Shreyankkkkk/foundations/projects/sumo-robot/notes/chat-summaries/INDEX.md

# Sumo chat summaries: index

Raw summaries (as generated by the summary prompt, one file per account): `account-1-context.txt` (18 chats), `account-2-context.txt` (15 chats). Both files are in this folder, unchanged except for any personal lines removed by hand.
`Order` is inferred from cross-references, not dates. Fill `Date` from the chat sidebar, then move the matching LOG.md lines into the dated section.
ID = account + position in that account's file.

| Order | ID | Chat title | Phase | Date |
|---|---|---|---|---|
| 1 | A1-10 | SumoX-26 Robot Planning | 1 planning | |
| 2 | A1-09 | SumoX-26 robot coding intro | 1 planning | |
| 3 | A1-01 | SumoX-26 Parts List & Sourcing | 1 planning | |
| 4 | A2-01 | Sumo Robot Strategy Selection | 1 planning | |
| 5 | A2-02 | Sumo robot GitHub research kickoff | 1 planning | |
| 6 | A1-02 | Sumo robot prep review | 1 planning | |
| 7 | A1-08 | SumoX-26 UNO Q wiring map | 2 wiring | |
| 8 | A1-03 | SumoX-26 constants and file architecture | 2 wiring | |
| 9 | A1-07 | SumoX-26 UNO Q firmware | 2 wiring | |
| 10 | A2-03 | SumoX-26 code audit & fixes | 3 Hybrid | |
| 11 | A2-04 | SumoX-26 firmware audit & merge | 3 Hybrid | |
| 12 | A1-04 | SumoX-26 code review and rewrite | 3 Hybrid | |
| 13 | A1-05 | SumoX-26 firmware review | 3 Hybrid | |
| 14 | A2-05 | SumoX-26 Code Audit | 3 Hybrid | |
| 15 | A1-06 | SumoX-26 firmware simulator | 3 Hybrid | |
| 16 | A1-11 | Sumo chassis STL audit and redesign | 3 Hybrid | |
| 17 | A2-06 | SumoX-26 firmware review and overhaul | 4 sensors | |
| 18 | A1-12 | Sumo robot sensor audit | 4 sensors | |
| 19 | A1-13 | SumoX-26 code audit and sensor calibration | 4 sensors | |
| 20 | A2-07 | Sumo IR sensor calibration | 4 sensors | |
| 21 | A2-08 | GP2Y0A21 calibration and filtering | 4 sensors | |
| 22 | A1-14 | TCRT5000 edge sensor bring-up | 4 sensors | |
| 23 | A2-09 | SumoX-26 v4 code overhaul | 5 v4 Ram | |
| 24 | A1-15 | SumoX-26 ram code review | 5 v4 Ram | |
| 25 | A2-10 | Sumo robot code audit + sensor bring-up | 5 v4 Ram | |
| 26 | A2-11 | Multi-file Arduino sketch deploy | 5 v4 Ram | |
| 27 | A2-12 | Sumo robot code Q&A prep | 5 v4 Ram | |
| 28 | A2-13 | Sumo robot code review | 5 v4 Ram | |
| 29 | A1-16 | SumoX-26 sumo robot, v4 fixes to v5 build | 6 v5 / v2.x | |
| 30 | A2-14 | Sumo robot code and strategy | 6 v5 / v2.x | |
| 31 | A2-15 | Sumo robot code audit and deploy | 6 v5 / v2.x | |
| 32 | A1-17 | SumoX-26 software finalization | 6 v5 / v2.x | |
| 33 | A1-18 | BlindSumo v2.4 to blind strategy | 6 v5 / v2.x | |

Archive rule: keep the old chats until this folder, LOG.md, STATE.md and Retrospective.md are committed and pushed.
