Shreyankkkkk/foundations/certificates/robotics/besomi-sumo-robot-workshop.pdf

# CERTIFICATE

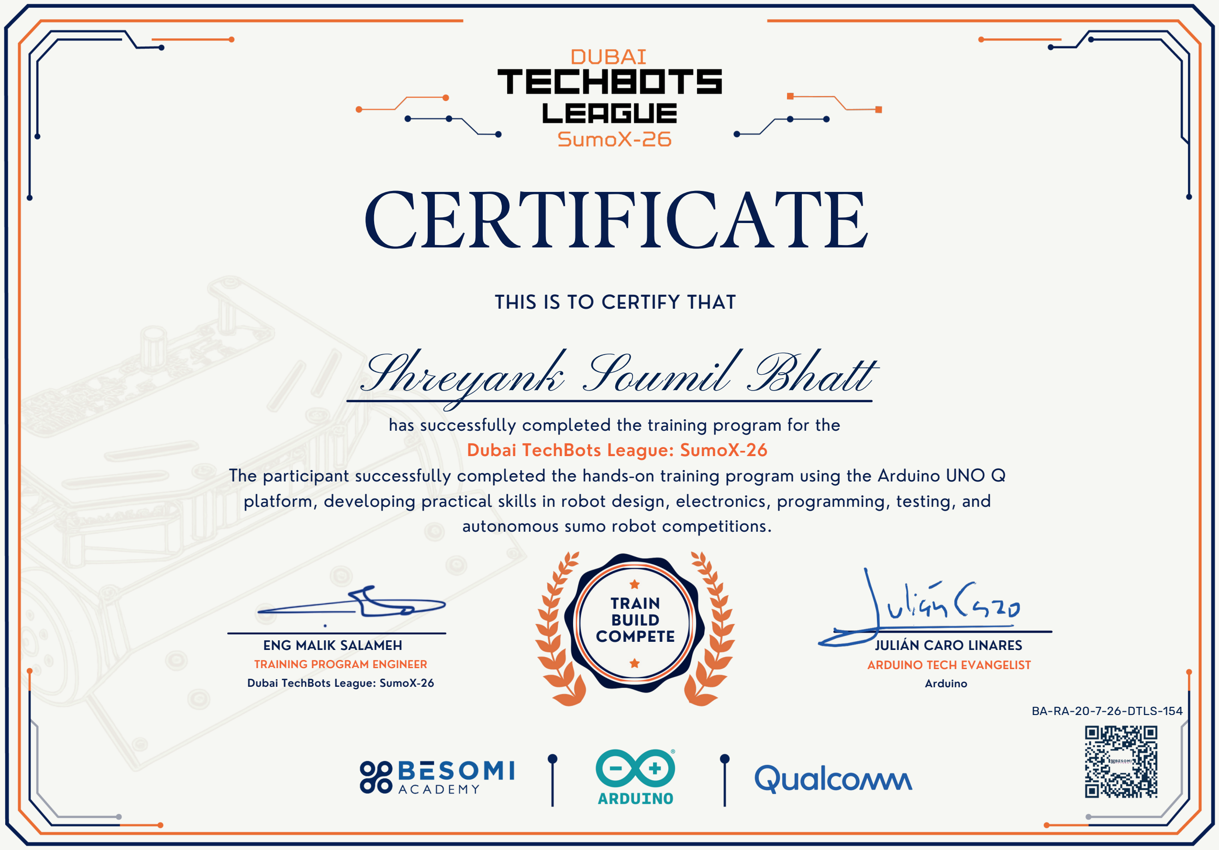
[picture p3: page 1]

TRAIN
BUILD
COMPETE

TRAINING PROGRAM ENGINEER
Dubai TechBots League: SumoX-26 | Arduino
ENG MALIK SALAMEH | JULIÁN CARO LINARES
| ARDUINO TECH EVANGELIST

THIS IS TO CERTIFY THAT

has successfully completed the training program for the Dubai TechBots League: SumoX-26 The participant successfully completed the hands-on training program using the Arduino UNO Q platform, developing practical skills in robot design, electronics, programming, testing, and autonomous sumo robot competitions.

BA-RA-20-7-26-DTLS-154

# Shreyank Soumil Bhatt
