Shreyankkkkk/foundations/projects/sumo-robot/docs/rulebook/Slides Sumo Robot - Dubai Techbots League SumoX-26.pdf

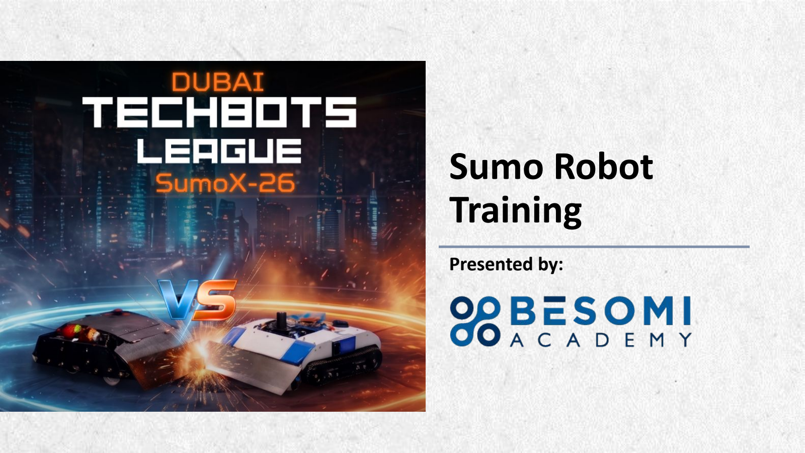
[picture p4: page 1]

# Sumo Robot Training

Presented by:

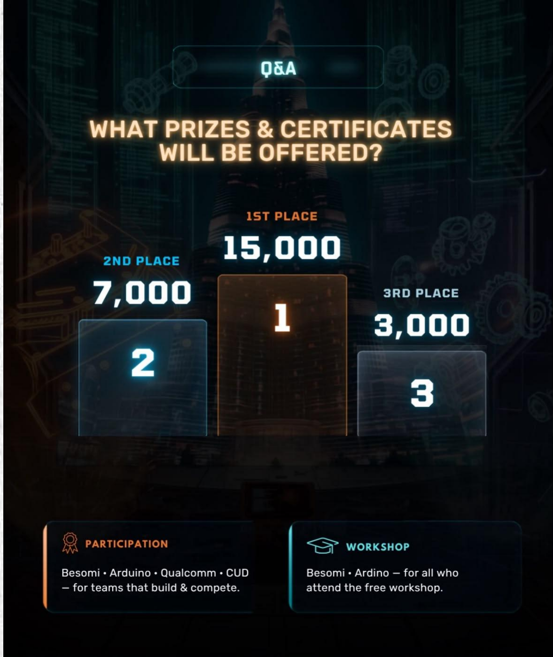
[picture p5: figure]

# Pool Prizes

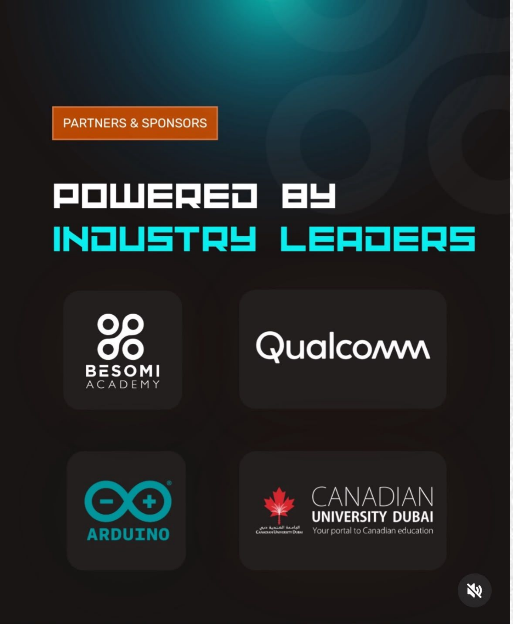
[picture p6: figure]

# POWERED BY

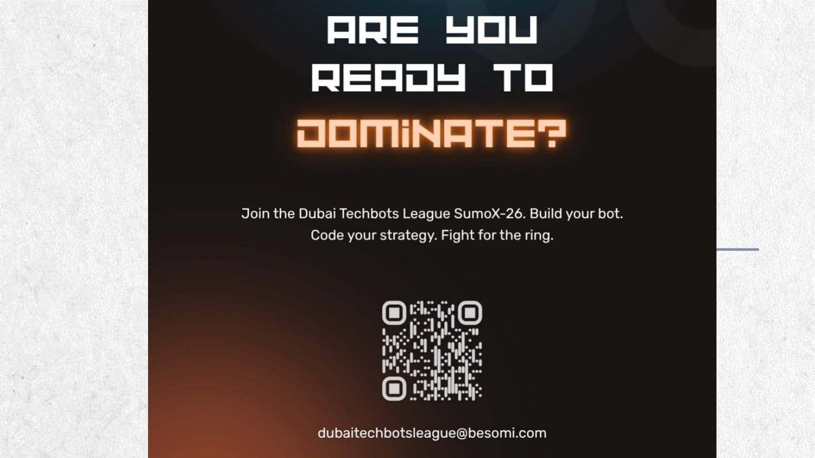
[picture p7: page 4]

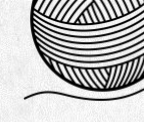
[picture p8: figure]

# LET’S PLAY THE WOOL BALL GAME AND THEN TEAM UP!

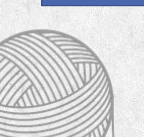
[picture p9: figure]

## WHAT IS SUMO ROBOTS?

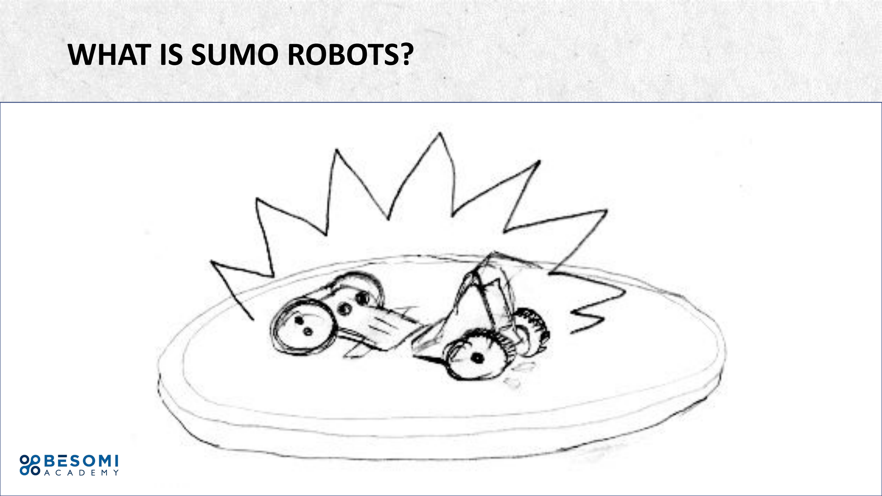
[picture p10: page 6]

## WHAT IS SUMO ROBOTS?

Robot Control: Autonomous and Remote-control

Engineering Principles: Torque, mechanical engineering, electrical engineering, computer science (for autonomous classes.)

Event Summary:
Two robots compete in a head-to-head match following the basic system of traditional human sumo matches. Robots are allowed no weapons, and are not allowed to flip each other. The sole purpose is a pushing match between the two robots to force the other from the arena. Multiple weight classes and control systems are allowed (autonomous compete against autonomous and R/C against R/C -they are separate classes and do not compete against each other.)

## WHAT IS SUMO ROBOTS?

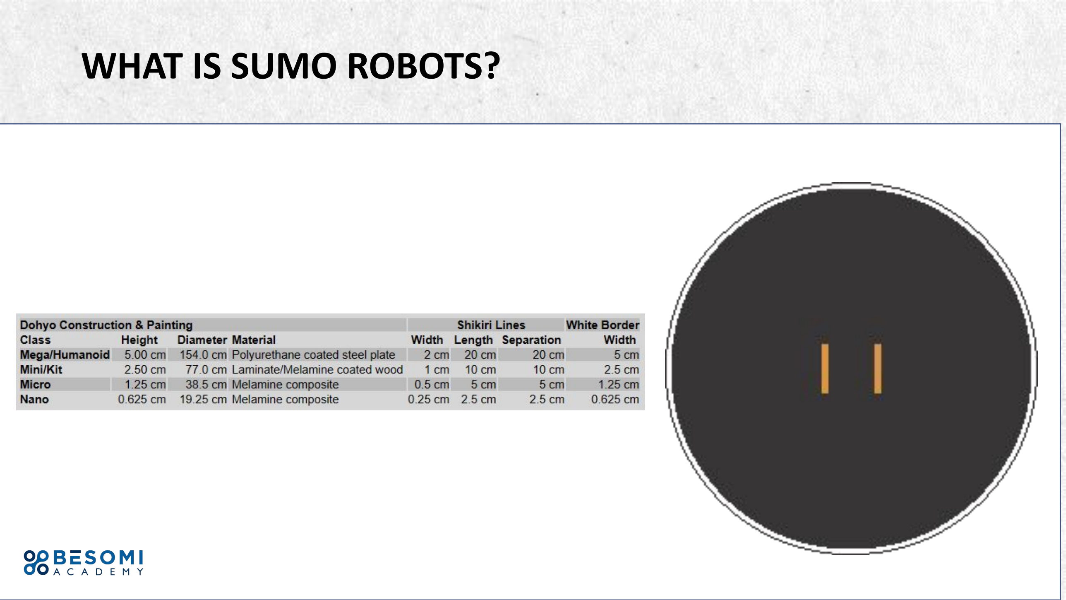
[picture p11: page 8]

## WHAT IS SUMO ROBOTS?

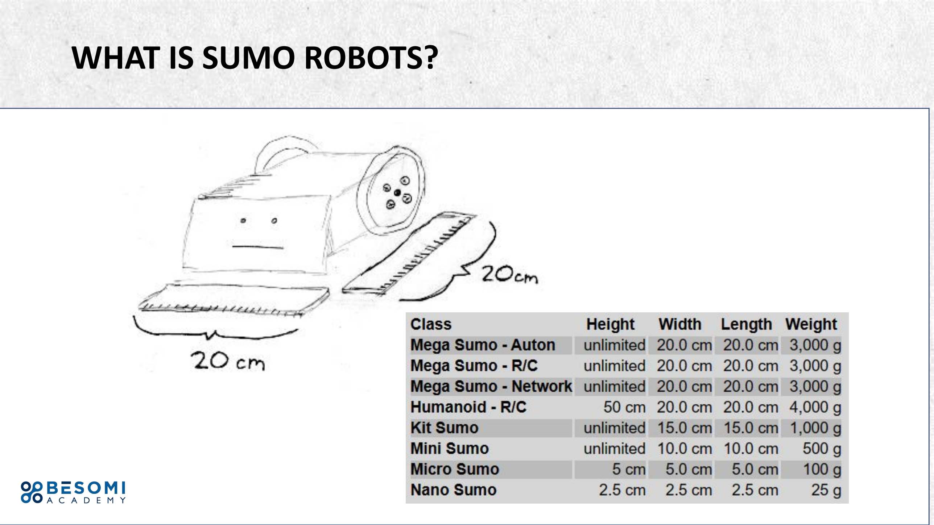
[picture p12: page 9]

## WHAT IS OUR GOAL?

To build an | | trying to fight
autonomous robot | that finds opponents
and push them | out of the ring, and | keep your robot inside the ring.

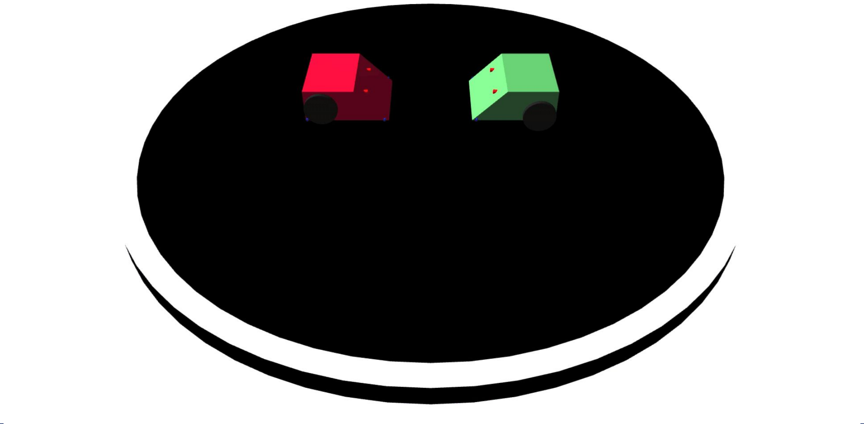
[picture p13: figure]

# What a Sumo Robot Needs?

## What a Sumo Robot Needs?

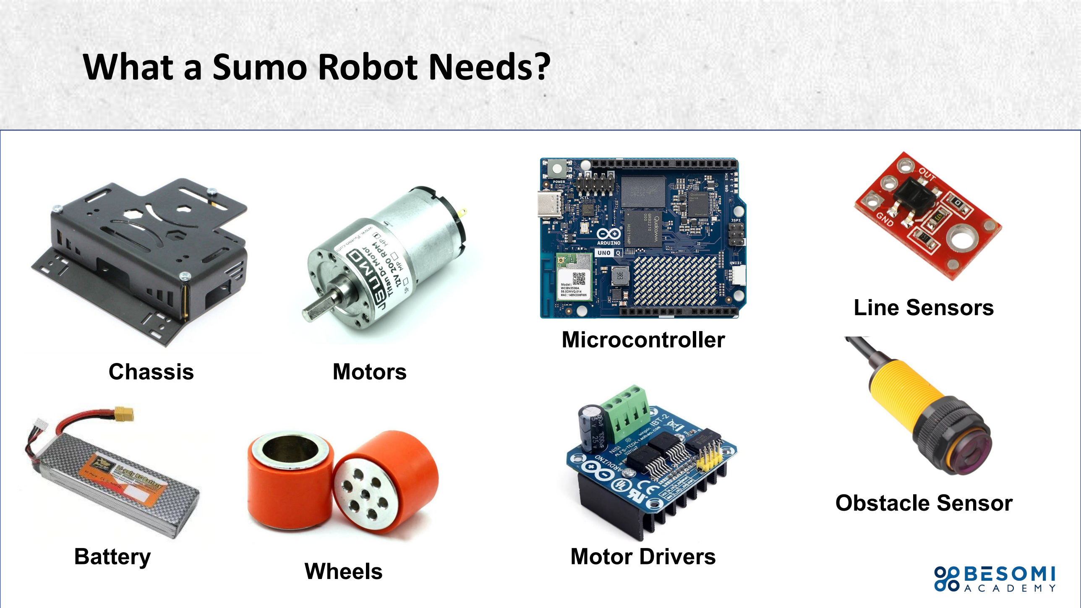
[picture p14: page 12]

Microcontroller

Obstacle Sensor

Line Sensors

Motor Drivers

Chassis

Wheels

Motors

Battery

## WHAT BRAIN TO CHOOSE?

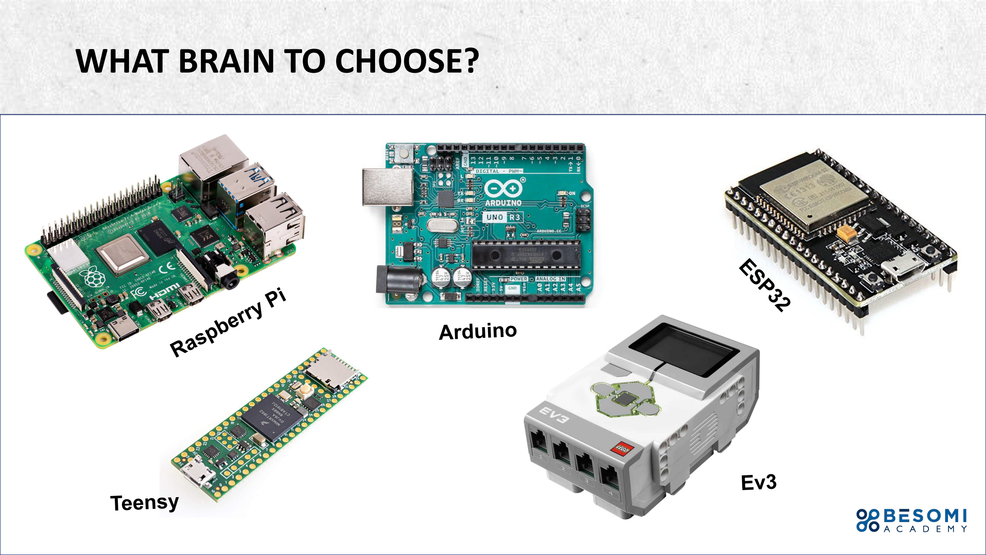
[picture p15: page 13]

Raspberry Pi

Teensy

Arduino

Ev3

ESP32

## TYPES OF ARDUINO BOARDS

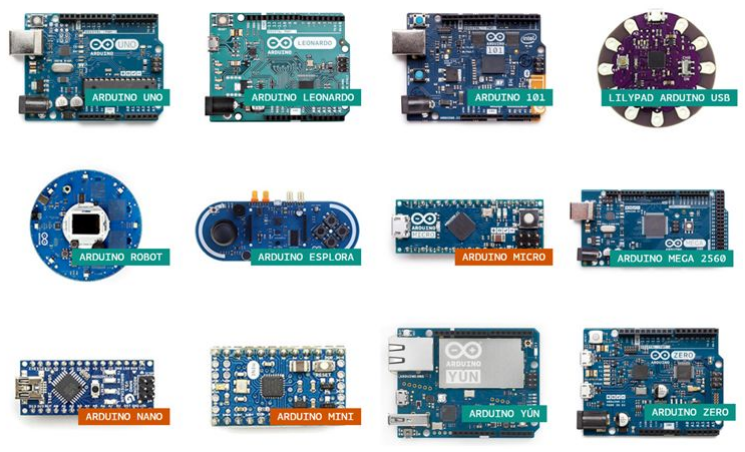
[picture p16: figure]

## OUR CHOICE

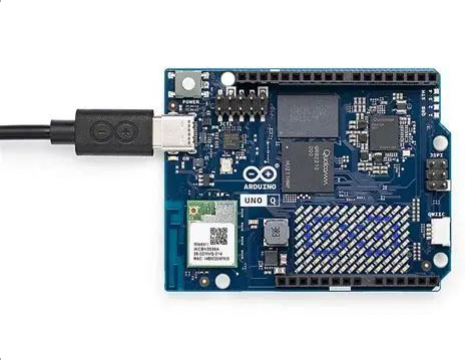
[picture p17: figure]

## Arduino UNO Q

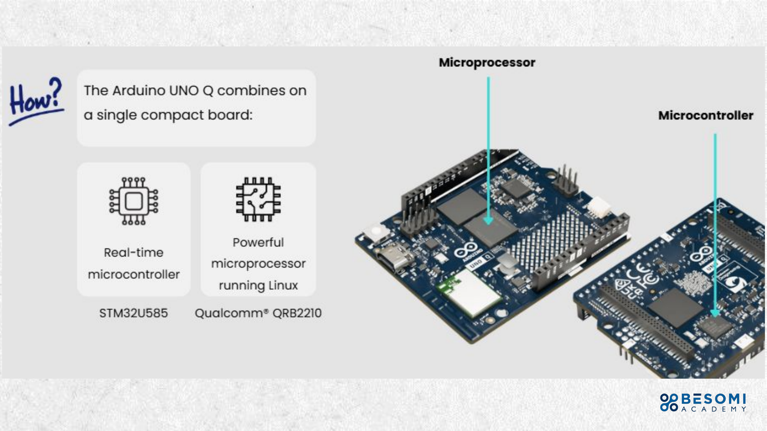
[picture p18: page 16]

## OUR CHOICE

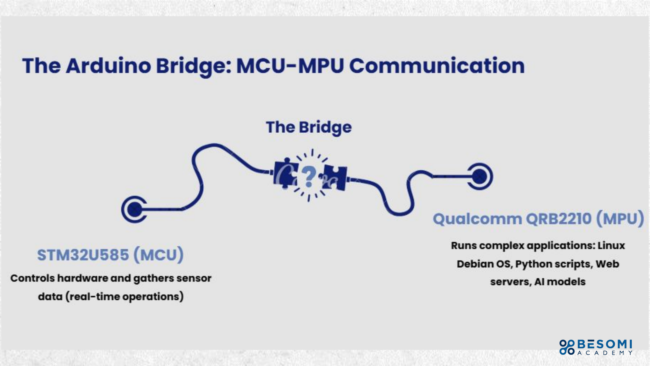
[picture p19: page 17]
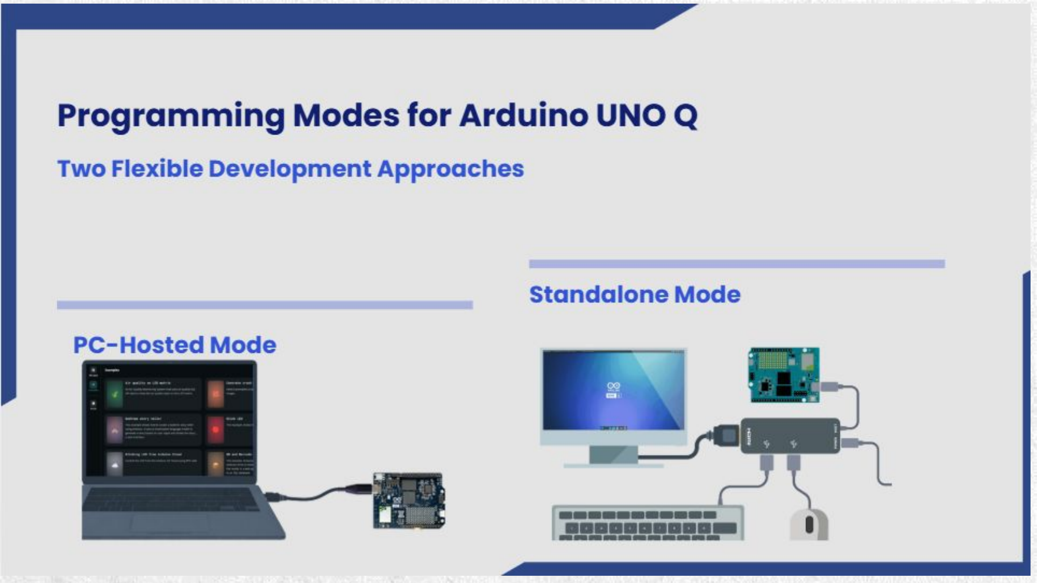
[picture p20: page 18]

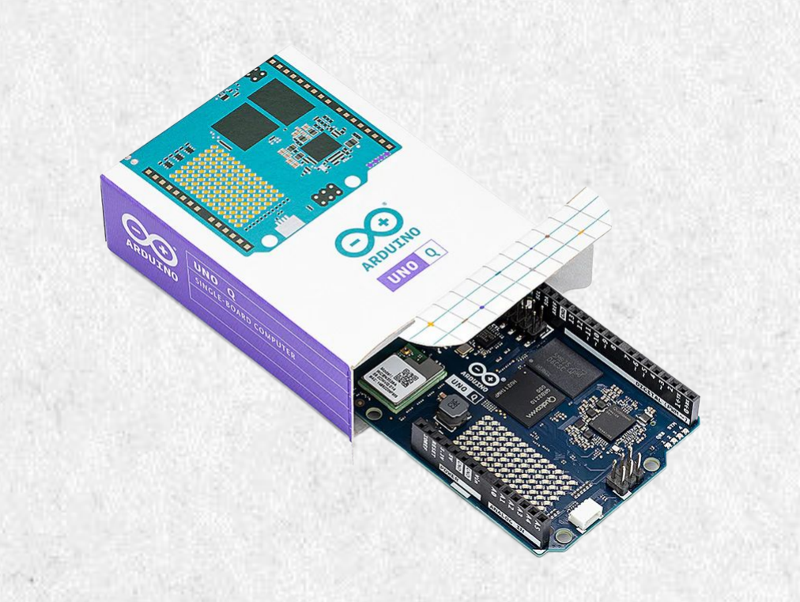
[picture p21: figure]

# WHAT IS ARDUINO?

Arduino is an open-source
electronics platform based on easy-to-use hardware
and software.

## APPLICATIONS OF ARDUINO

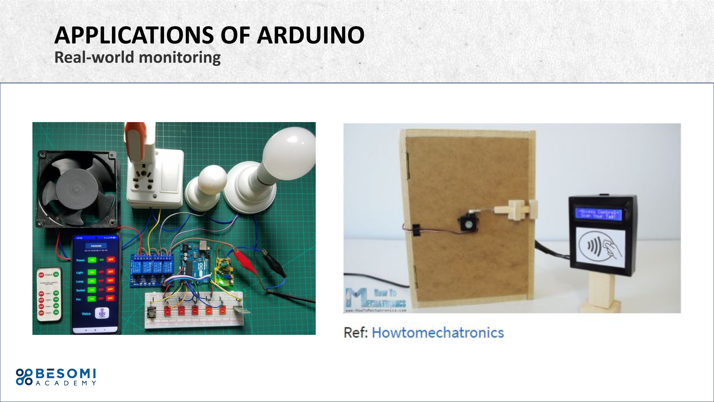
[picture p22: page 20]

Real-world monitoring

## APPLICATIONS OF ARDUINO

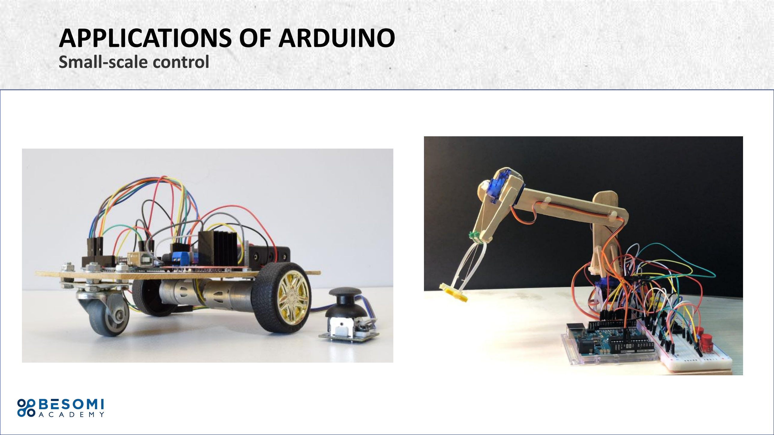
[picture p23: page 21]

Small-scale control

## APPLICATIONS OF ARDUINO

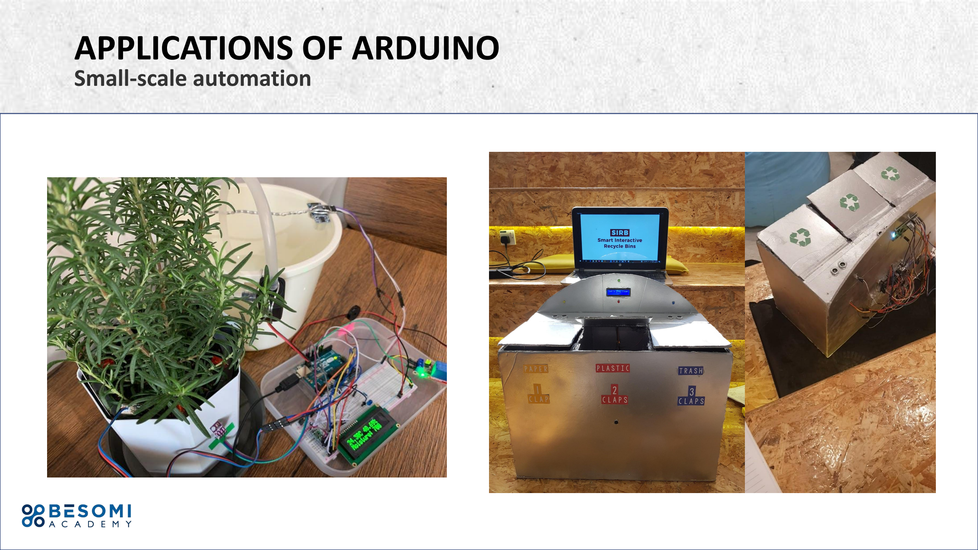
[picture p24: page 22]

Small-scale automation

## APPLICATIONS OF ARDUINO

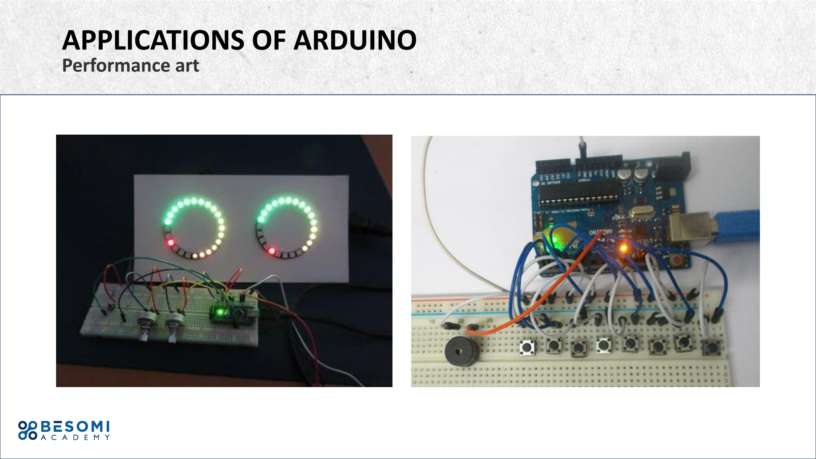
[picture p25: page 23]

Performance art

## TWO WAYS TO PRACTICE WITH US

1

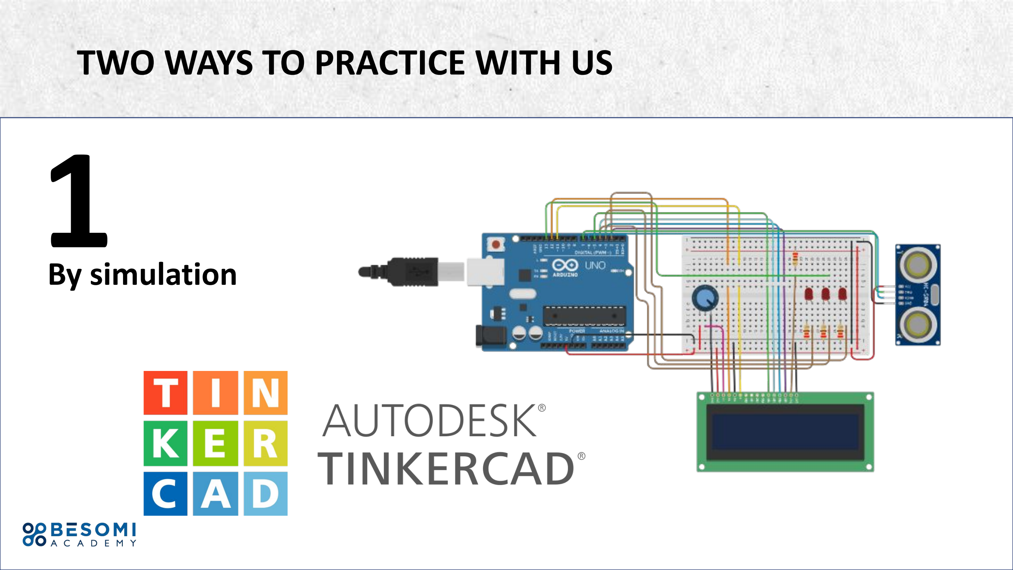
[picture p26: page 24]

## By simulation

## TWO WAYS TO PRACTICE WITH US

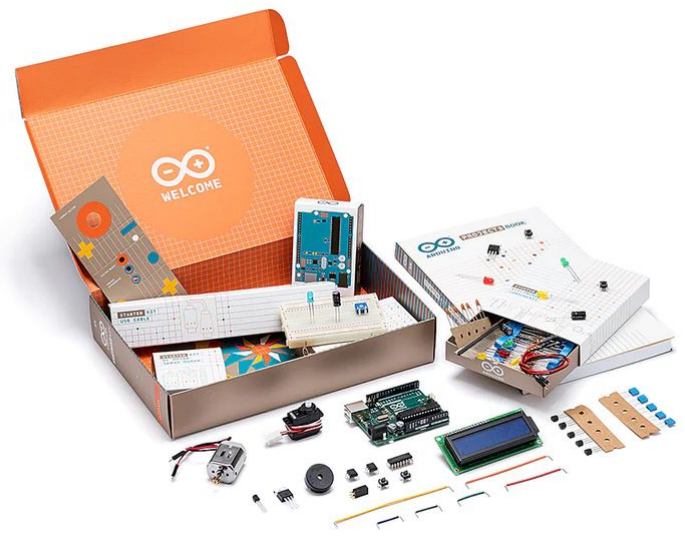
[picture p27: figure]

2

## Physically by hands

## CODING USING ARDUINO IDE

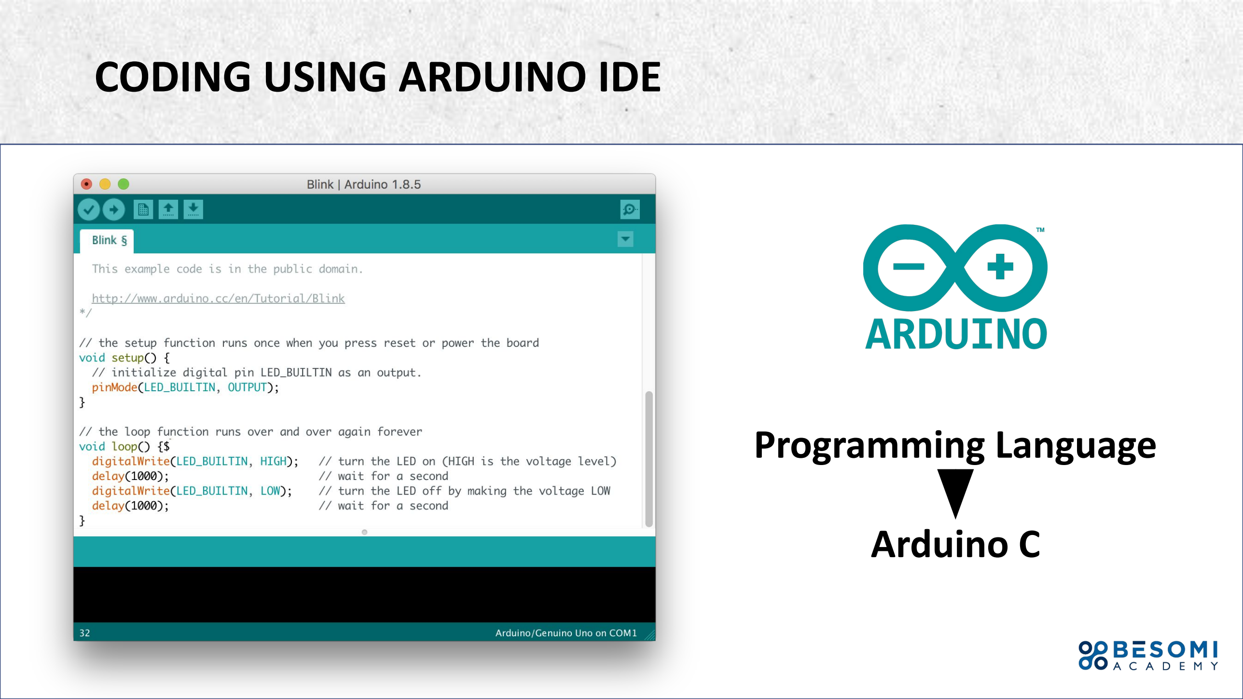
[picture p28: page 26]

## Programming Language

## Arduino C

## Arduino App Lab

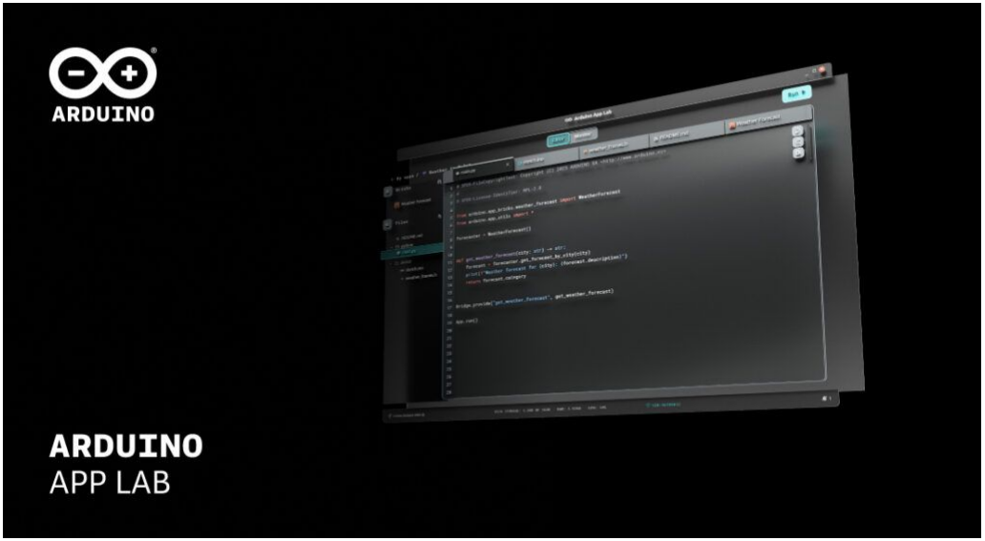
[picture p29: figure]
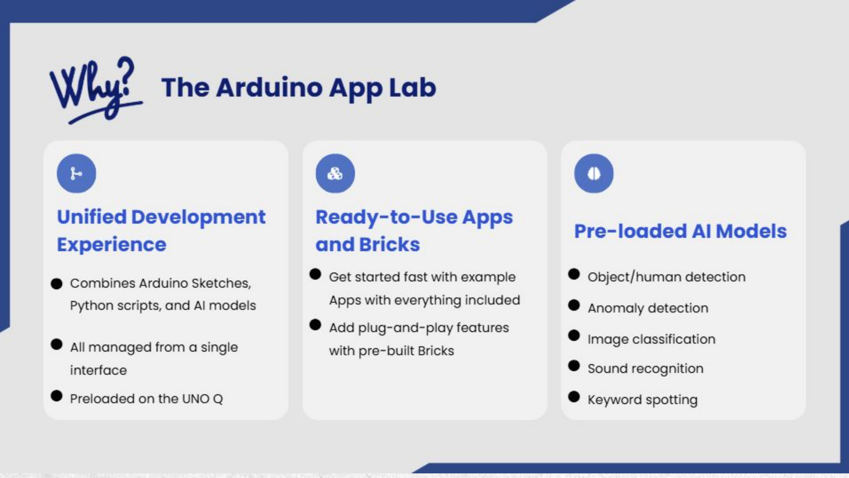
[picture p30: page 28]

# Inputs vs Outputs

## INPUT

VS

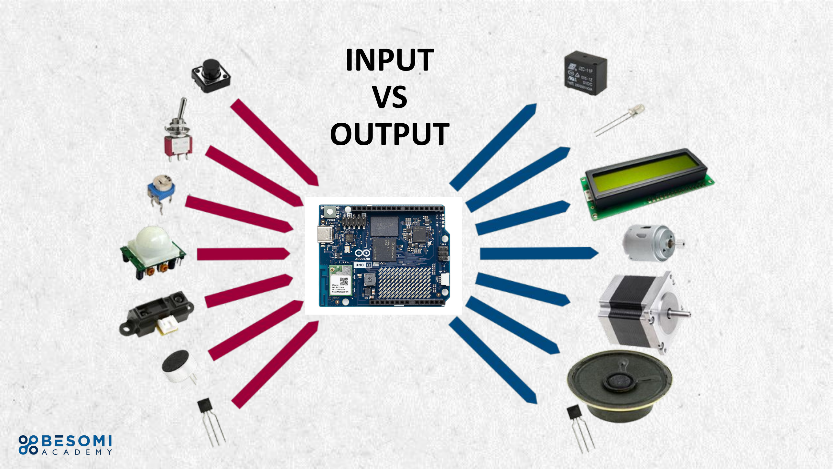
[picture p31: page 30]

## OUTPUT

## INPUT OR OUTPUT?

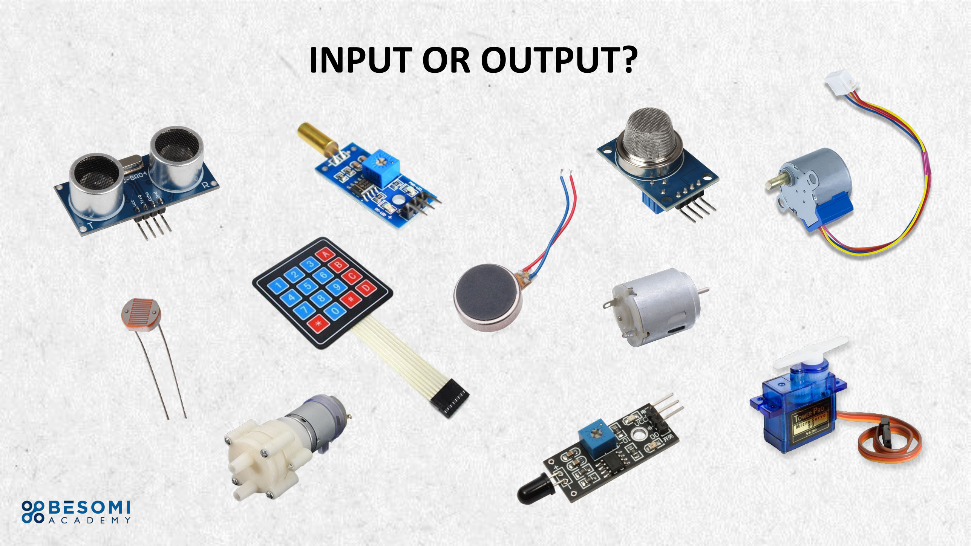
[picture p32: page 31]

# LET’S GET DEEPER

# 3 WAYS TO POWER THE ARDUINO BOARD

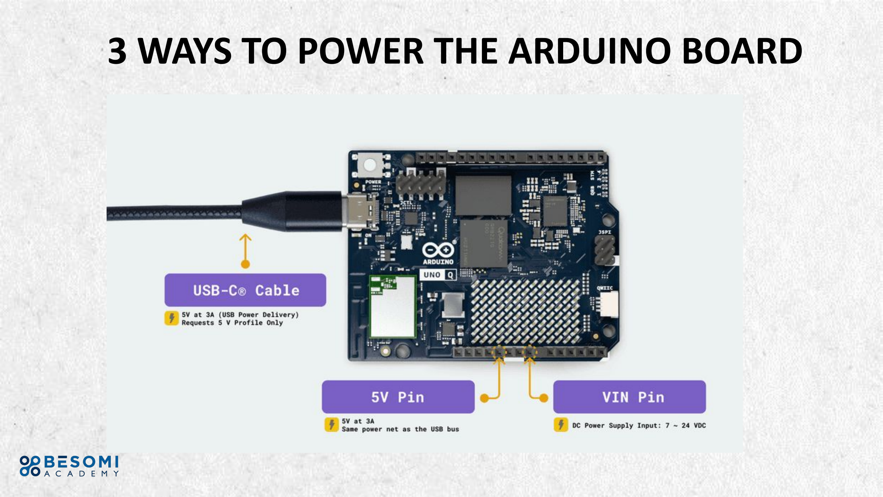
[picture p33: page 33]

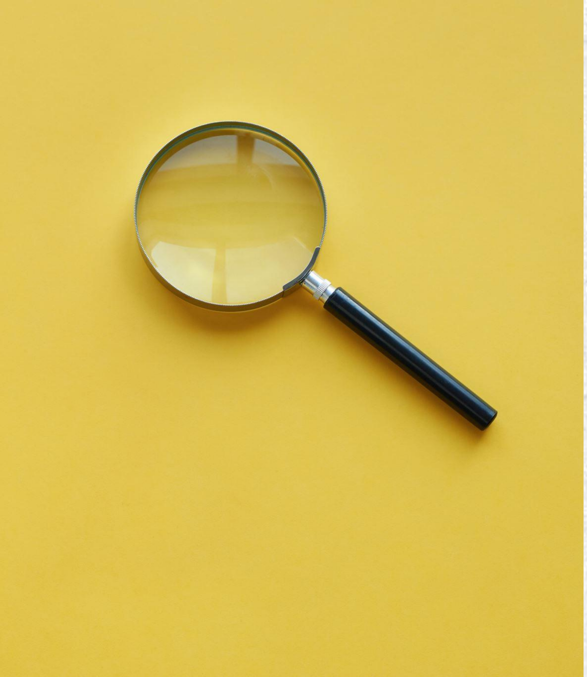
[picture p34: figure]

# FEW THINGS WE SHOULD KNOW ABOUT

## THE BREADBOARD

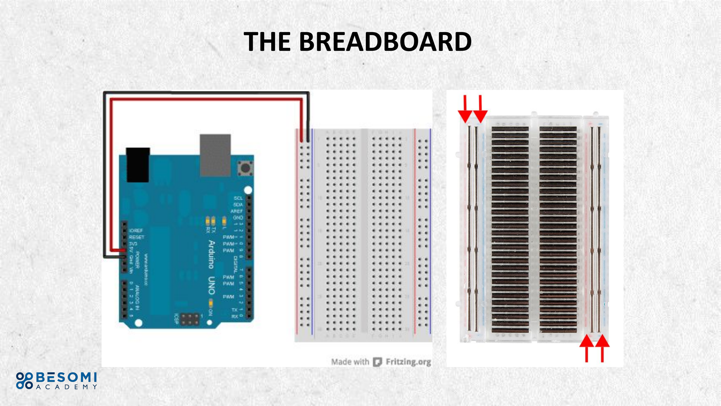
[picture p35: page 35]

# JUMPER WIRES

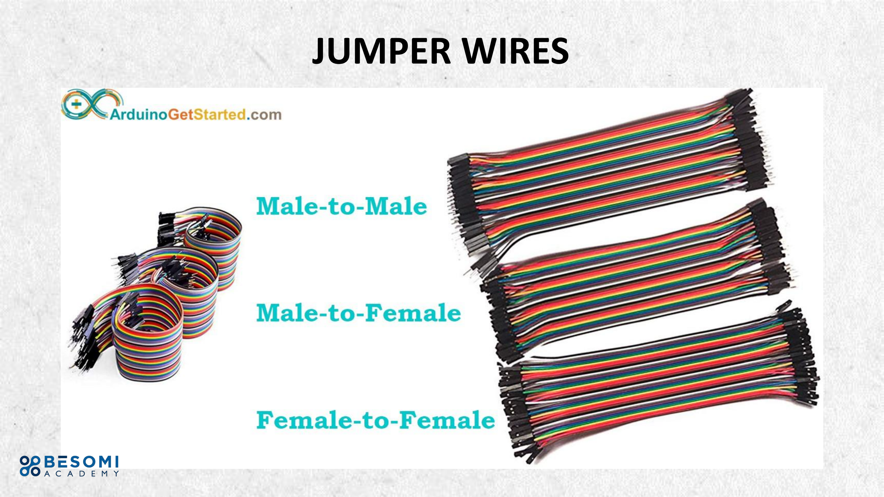
[picture p36: page 36]

## ANODE & CATHODE

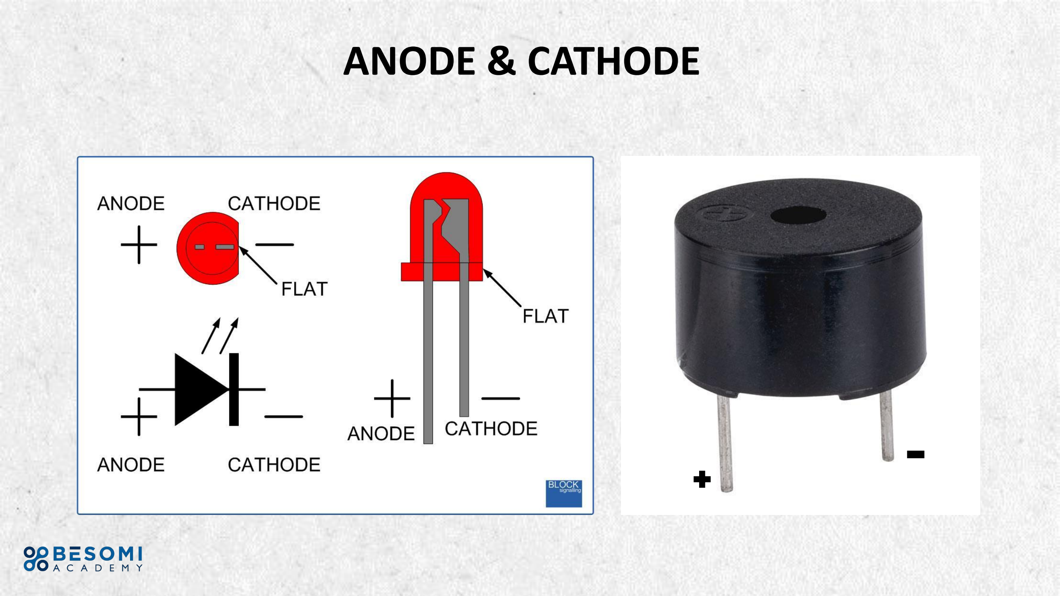
[picture p37: page 37]

## RESISTORS

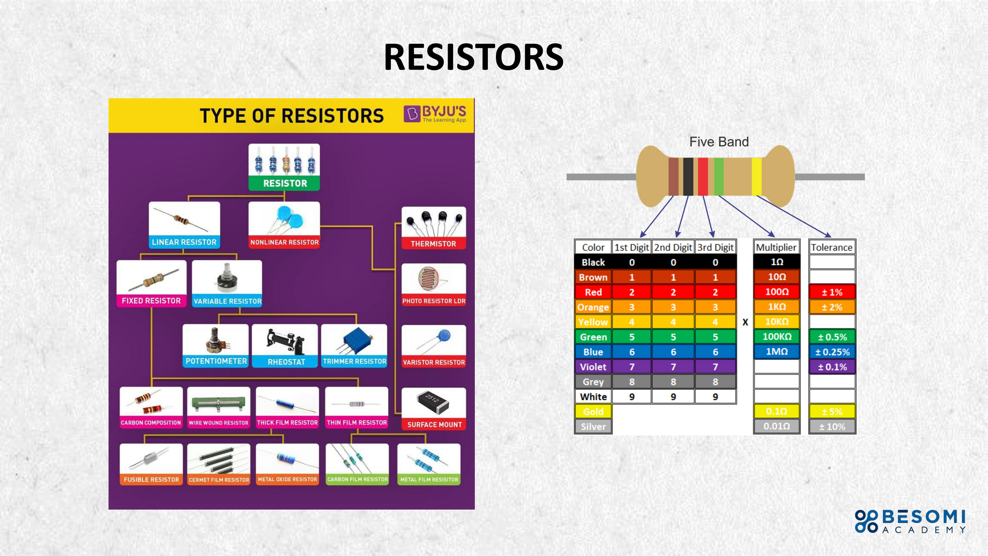
[picture p38: page 38]

# DIGITAL PINS

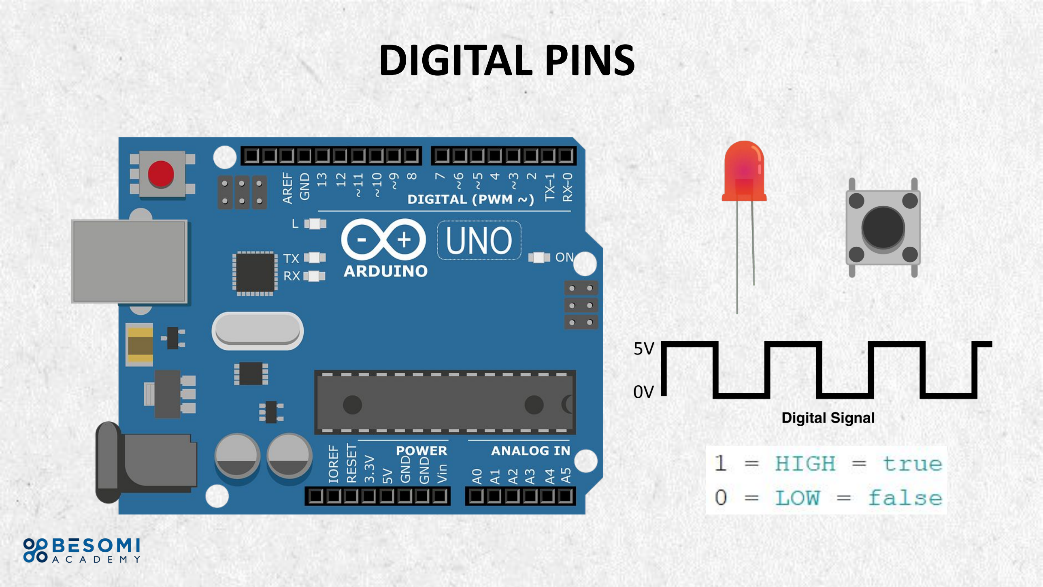
[picture p39: page 39]

5V

0V

# DIGITAL PINS

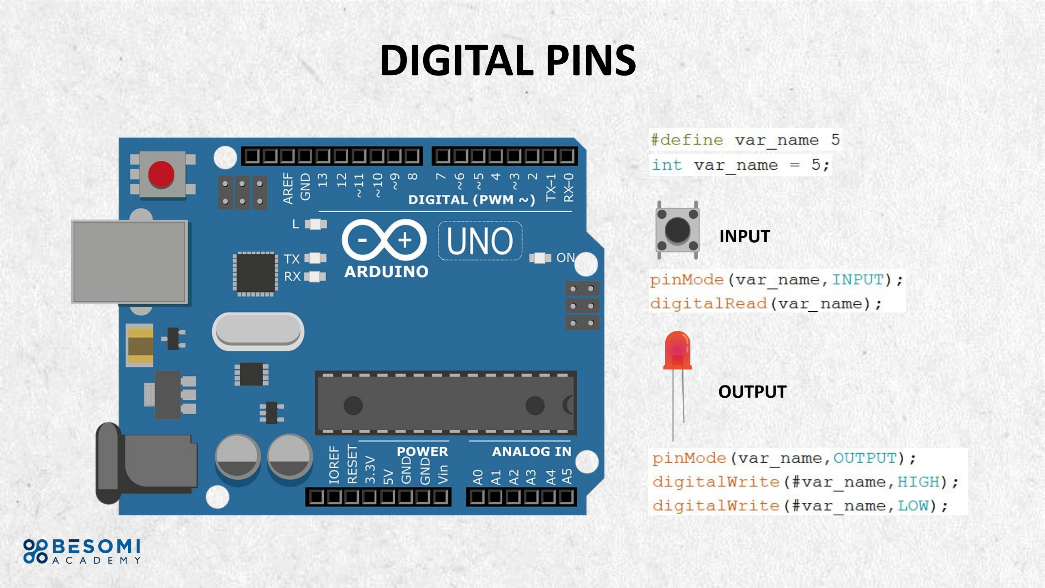
[picture p40: page 40]

INPUT

OUTPUT

_

# ANALOG PINS

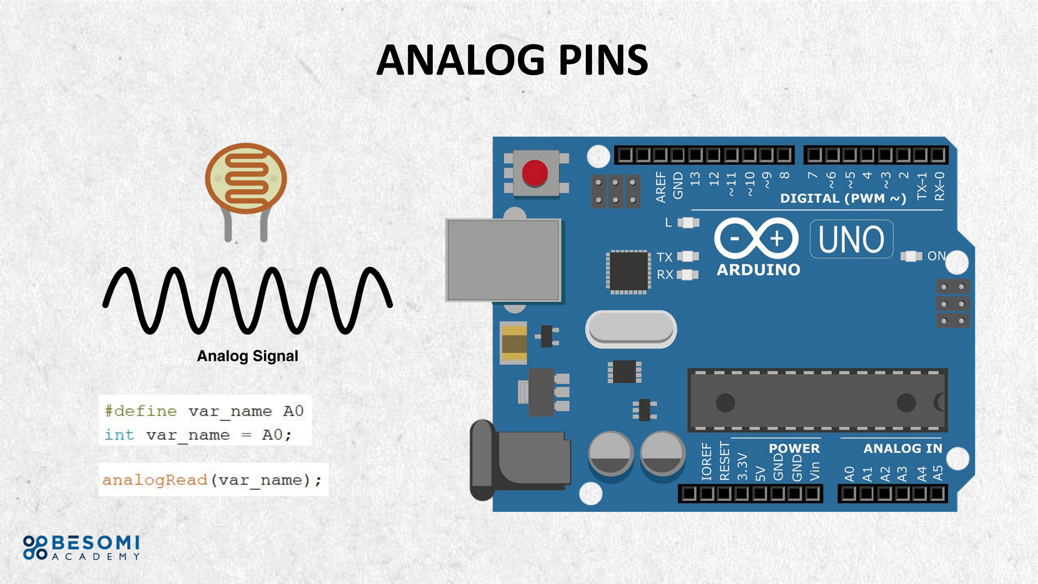
[picture p41: page 41]

# ANALOG PINS

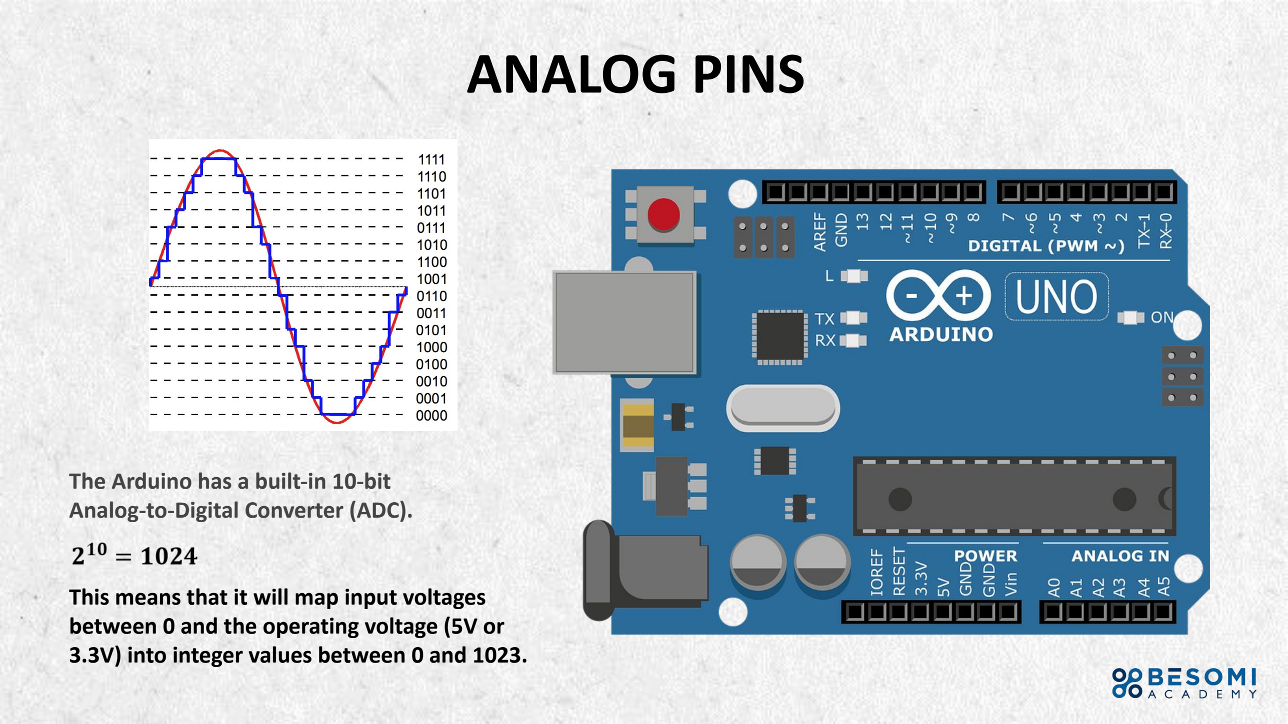
[picture p42: page 42]

The Arduino has a built-in 10-bit Analog-to-Digital Converter (ADC).

This means that it will map input voltages between 0 and the operating voltage (5V or 3.3V) into integer values between 0 and 1023.

## WHAT ABOUT GETTING ANALOG OUTPUT?

# PWM (PULSE WIDTH MODULATION)

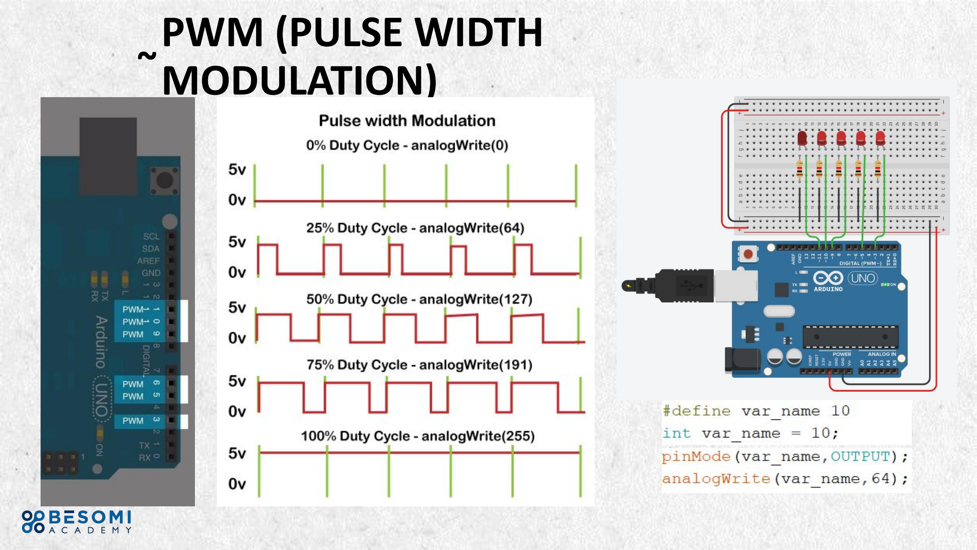
[picture p43: page 44]

~

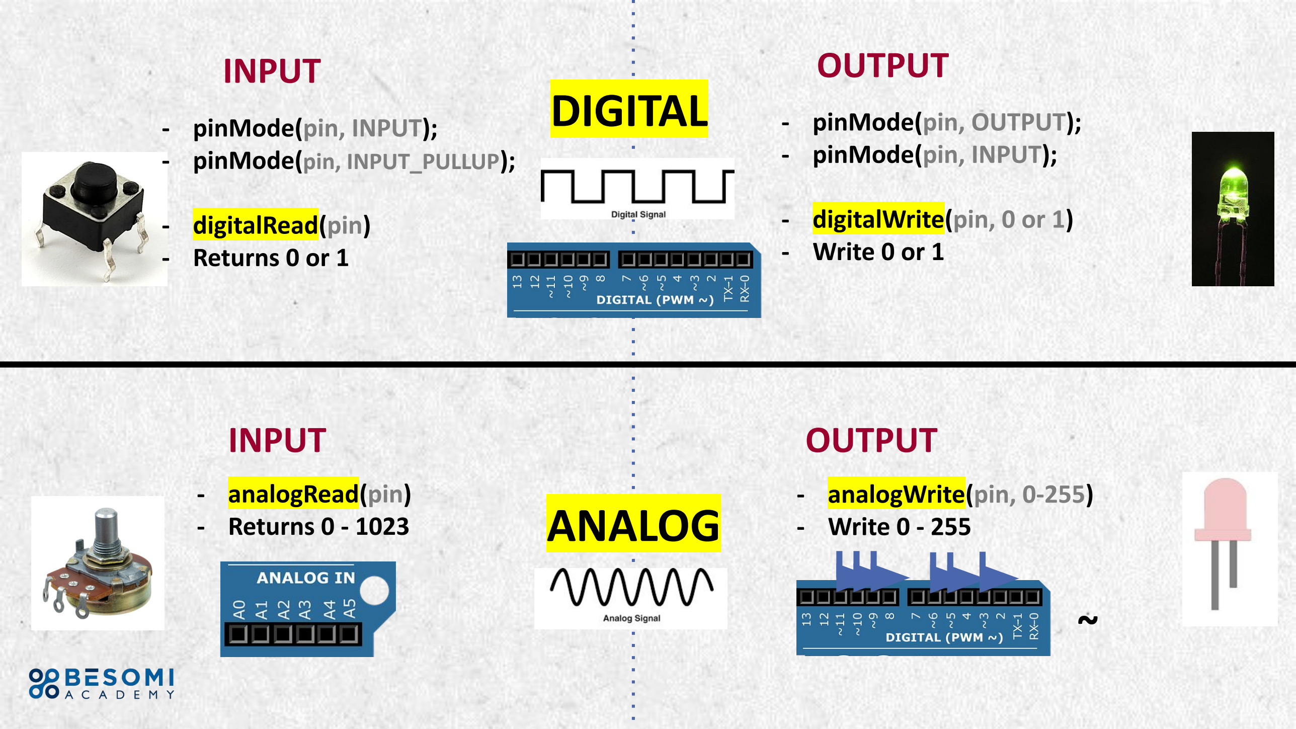
[picture p44: figure]
INPUT; DIGITAL; ANALOG; OUTPUT; - pinMode(pin, INPUT); - pinMode(pin, INPUT_PULLUP);; - digitalRead(pin) - Returns 0 or 1; - pinMode(pin, OUTPUT); - pinMode(pin, INPUT);; - digitalWrite(pin, 0 or 1) - Write 0 or 1; - analogRead(pin) - Returns 0 - 1023; - analogWrite(pin, 0-255) - Write 0 - 255

## MANY KINDS OF SENSORS

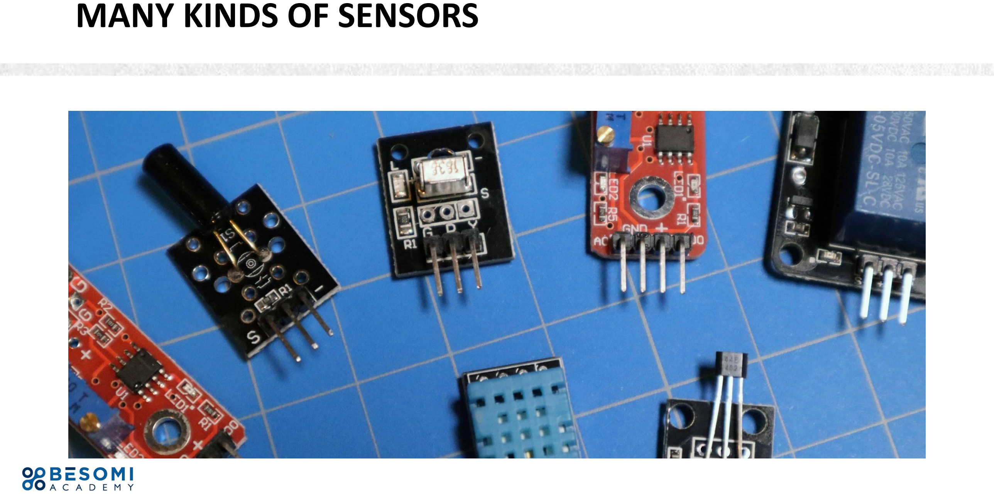
[picture p45: page 46]

## Types of Obstacle Sensors

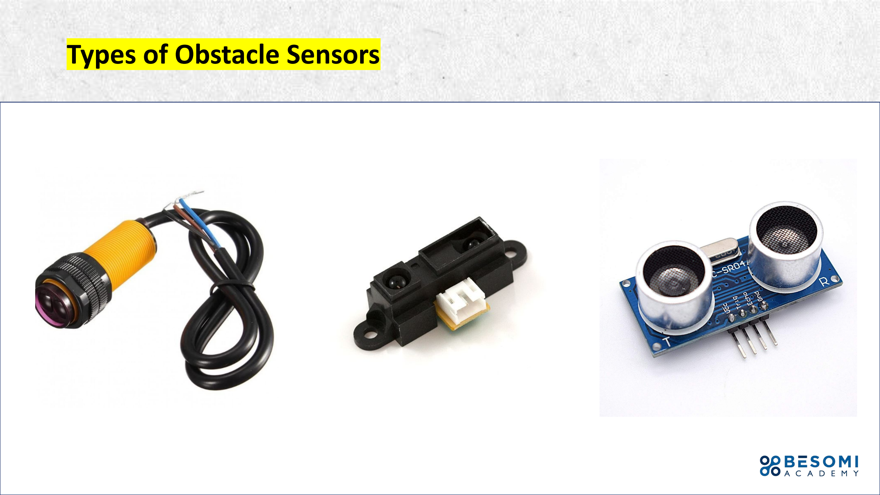
[picture p46: page 47]

## Types of Obstacle Sensors

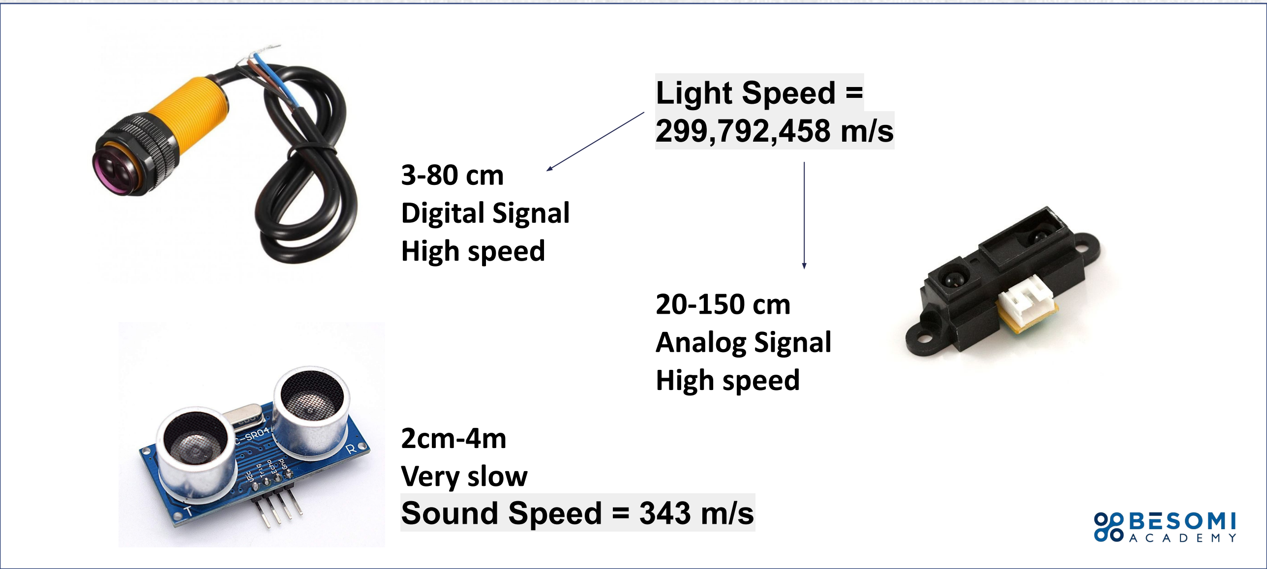
[picture p47: figure]
3-80 cm Digital Signal High speed; 20-150 cm Analog Signal High speed; 2cm-4m Very slow Sound Speed = 343 m/s; Light Speed = 299,792,458 m/s

## Obstacle Sensor (IR Sensor)

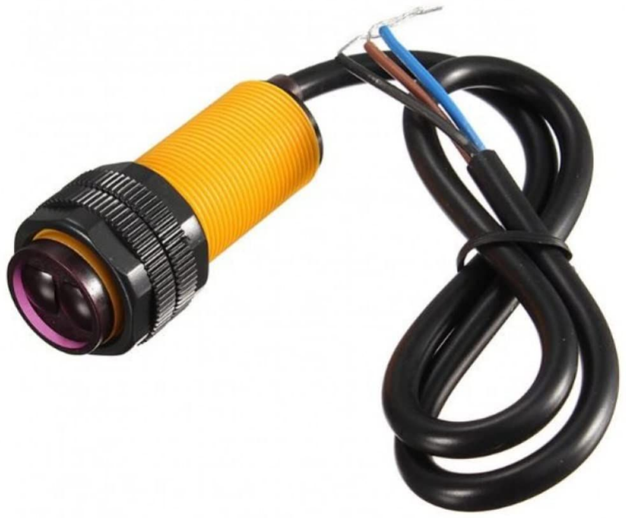
[picture p48: figure]

The E18-D80NK adjustable IR Infrared Proximity Sensor Switch features an IR sensor that can measure distance between 3 to 80 cm. The infrared proximity switch module is a reflection-type photoelectric sensor which integrates transmitting and receiving infrared beams function. Infrared proximity switches work by sending out beams of invisible infrared light.

## Obstacle Sensor (IR Sensor)

- Input voltage: 5V DC
- Current consumption: >25mA (min) > 100mA (max)
- Dimension: 1.7cm (diameter) x 4.5cm (length)
- Cable length: 45cm
- Detection of objects: transparent or Opaque
- Sensing range: 3cm-80cm
- NPN output: (normally high)
- Environment temperature: -25 degC ~ 55 degC

## Obstacle Sensor (IR Sensor)

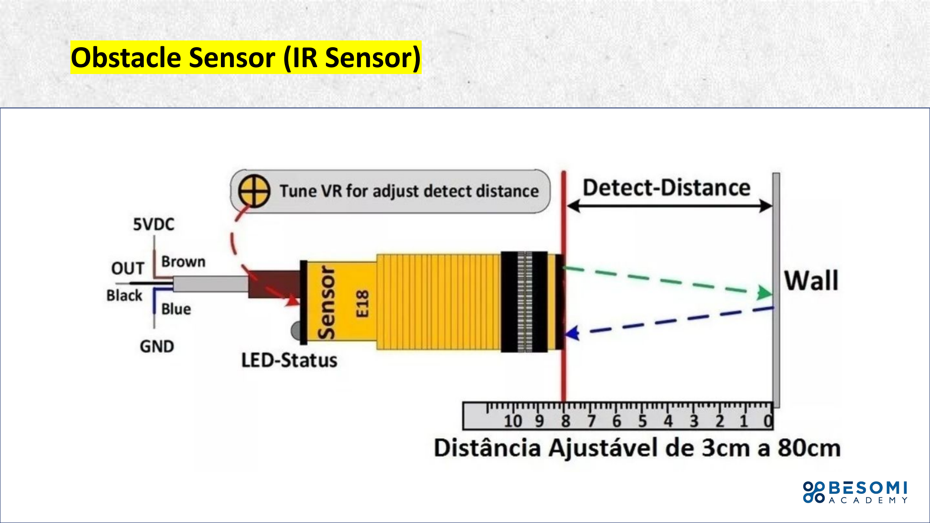
[picture p49: page 51]

## Obstacle Sensor (IR Sensor)

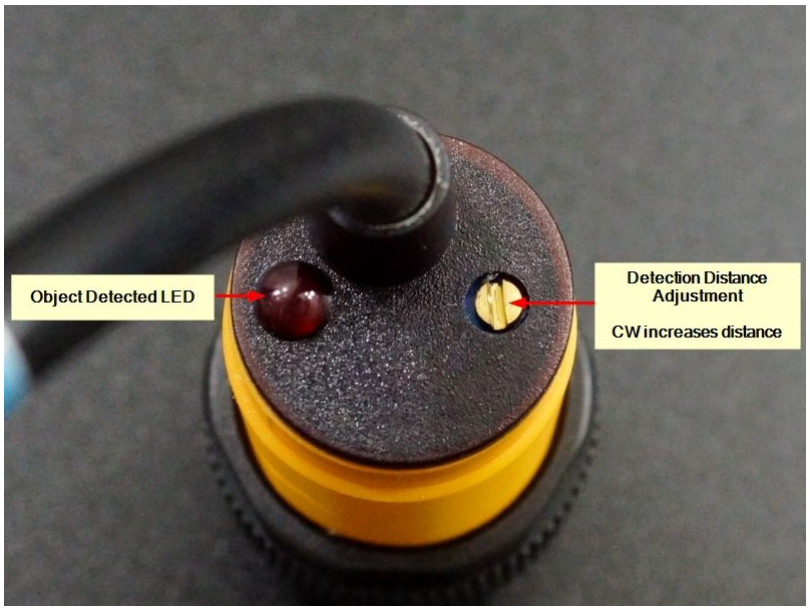
[picture p50: figure]

## Obstacle Sensor (IR Sensor)

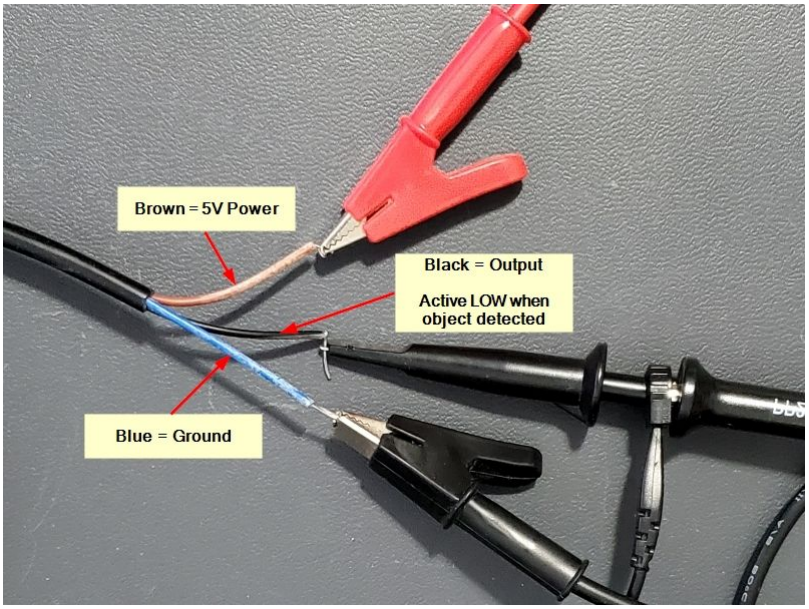
[picture p51: figure]

## Obstacle Sensor (IR Sensor)

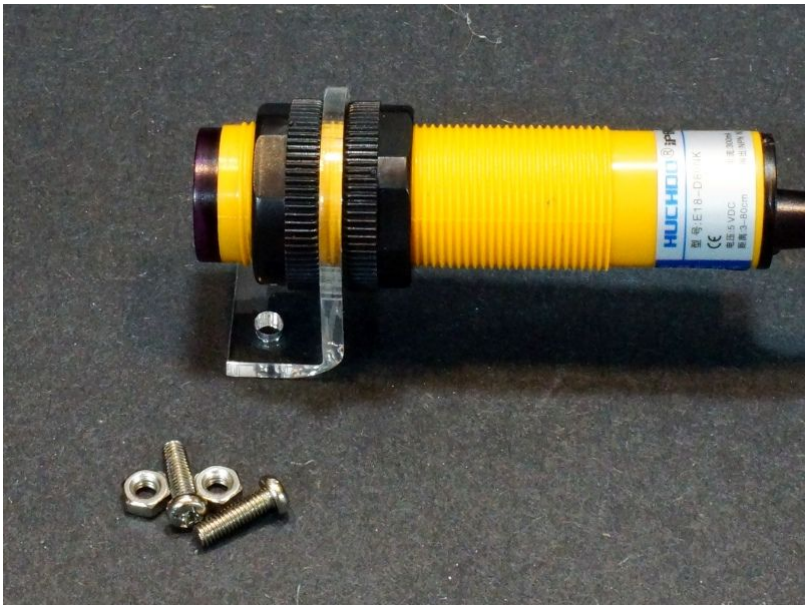
[picture p52: figure]

## Obstacle Sensor (IR Sensor)

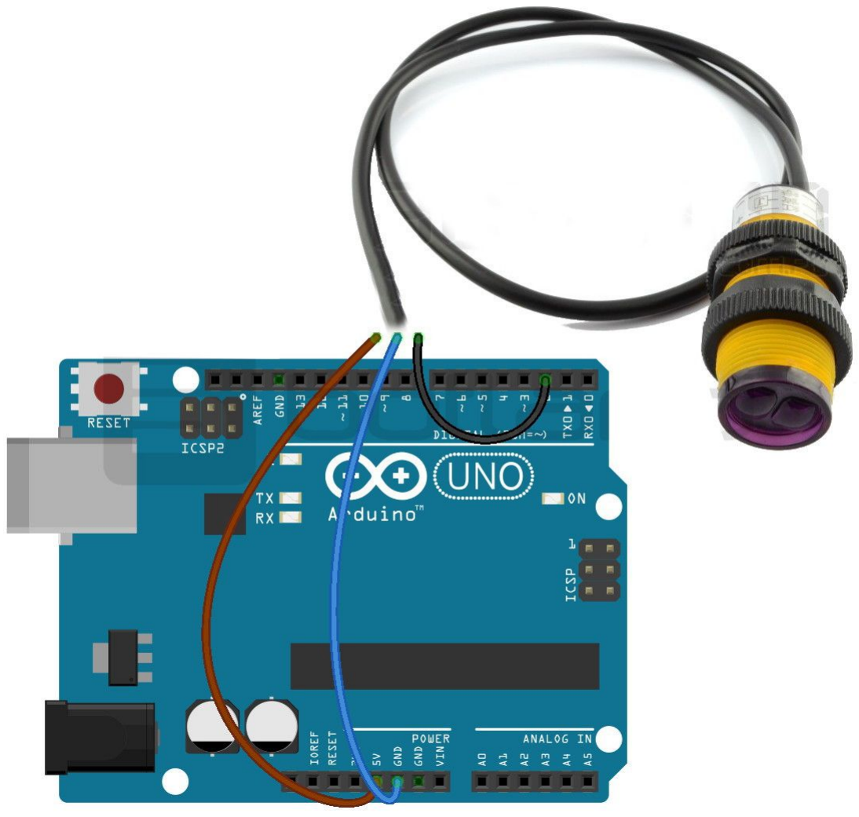
[picture p53: figure]

## Obstacle Sensor (IR Sensor)

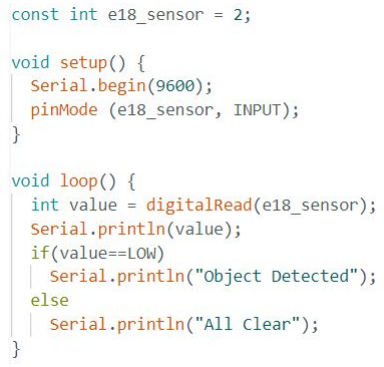
[picture p54: figure]

## Types of Black and White Sensors

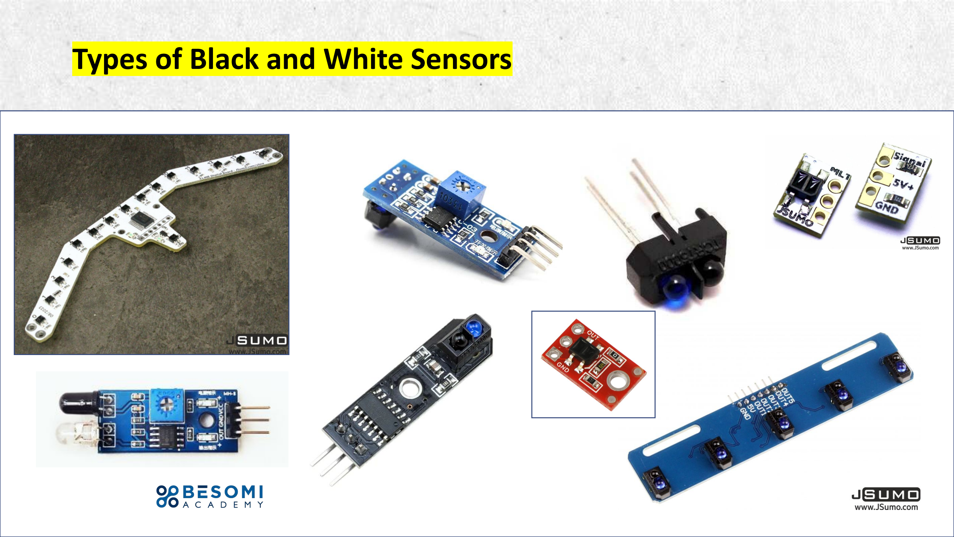
[picture p55: page 57]

## Types of Black and White Sensors

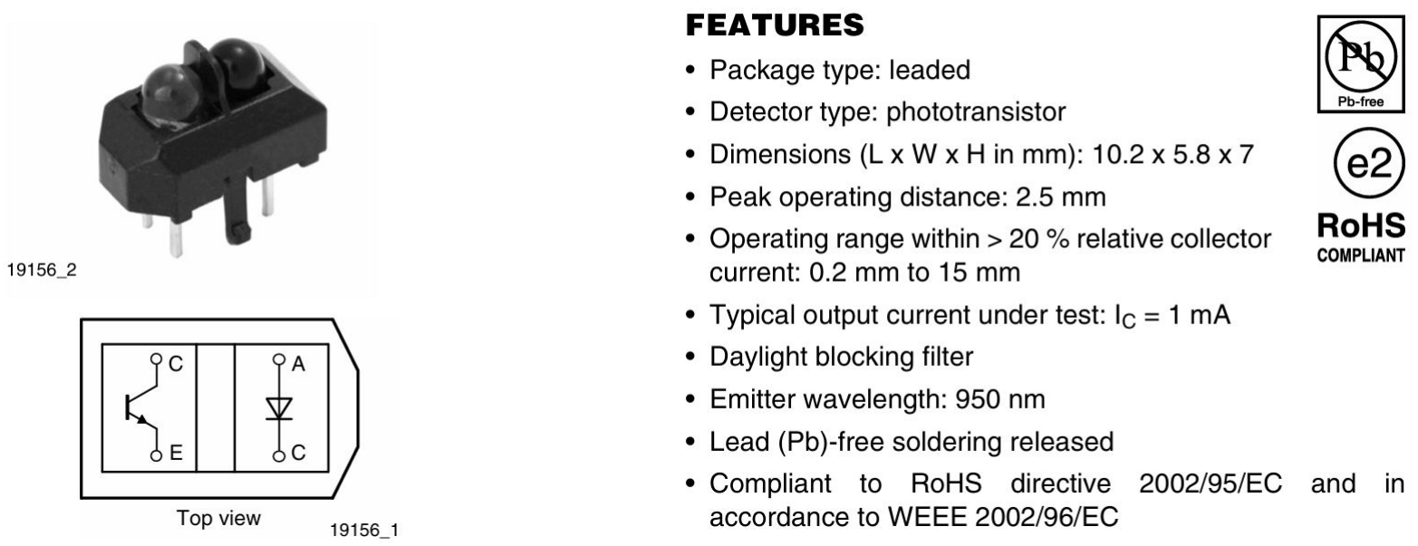
[picture p56: figure]

Response Time - Distance Range - Weight - Dimensions

## Black and White Sensor (IR SENSOR)

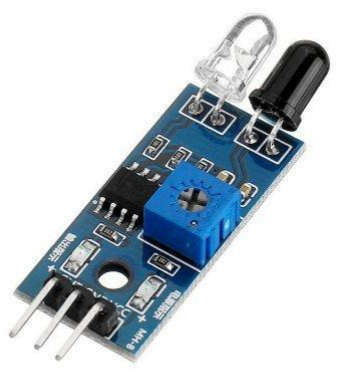
[picture p57: figure]

An infrared proximity sensor or IR Sensor is an electronic device that emits infrared lights to sense some aspect of the surroundings and can be employed to detect the motion of an object.

## Black and White Sensor (IR SENSOR)

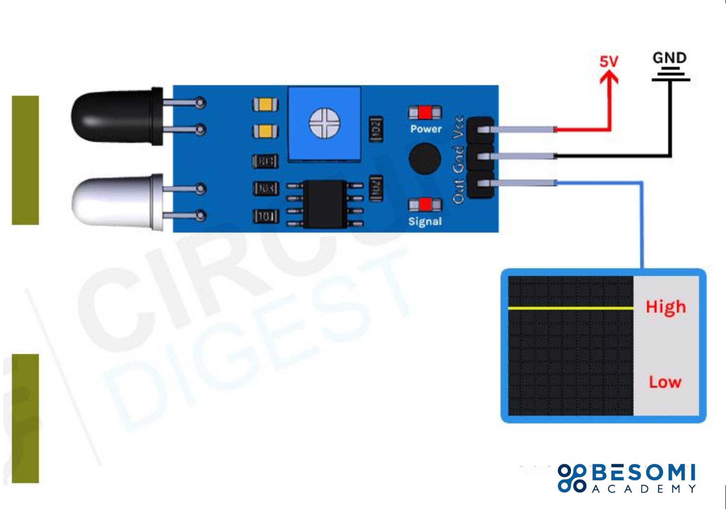
[picture p58: figure]

The OUT pin from the IR sensor outputs a LOW value when it receives a reflected IR signal, i.e. detected an object (white), and a HIGH value when it is not receiving a reflected IR signal, i.e. no object (black).

## Black and White Sensor (IR SENSOR)

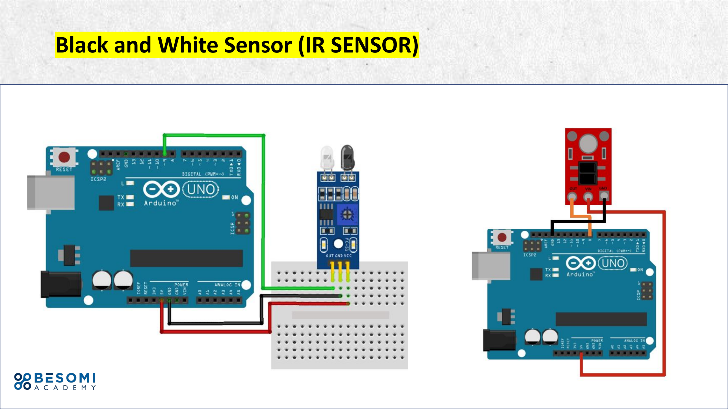
[picture p59: page 61]

## Black and White Sensor (IR SENSOR)

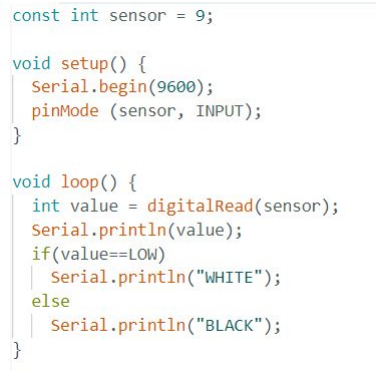
[picture p60: figure]
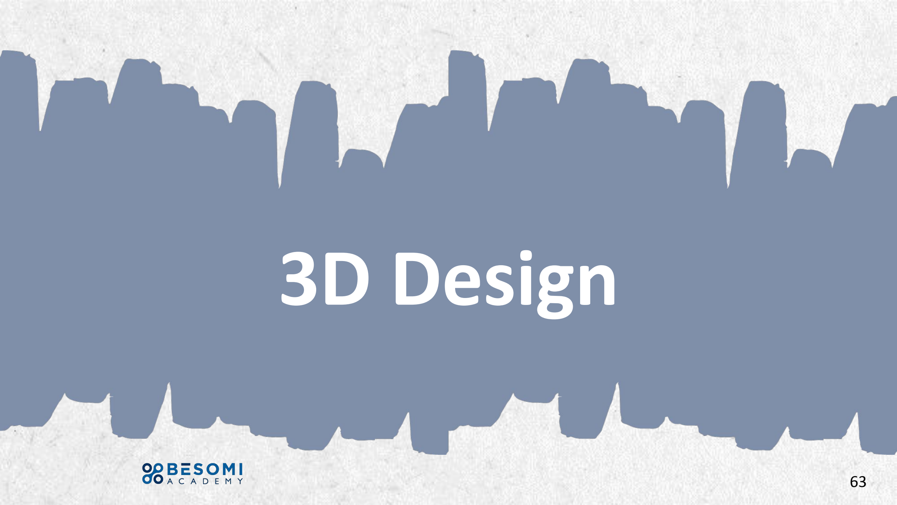
[picture p61: page 63]

63

# 3D Design

## 3D Design

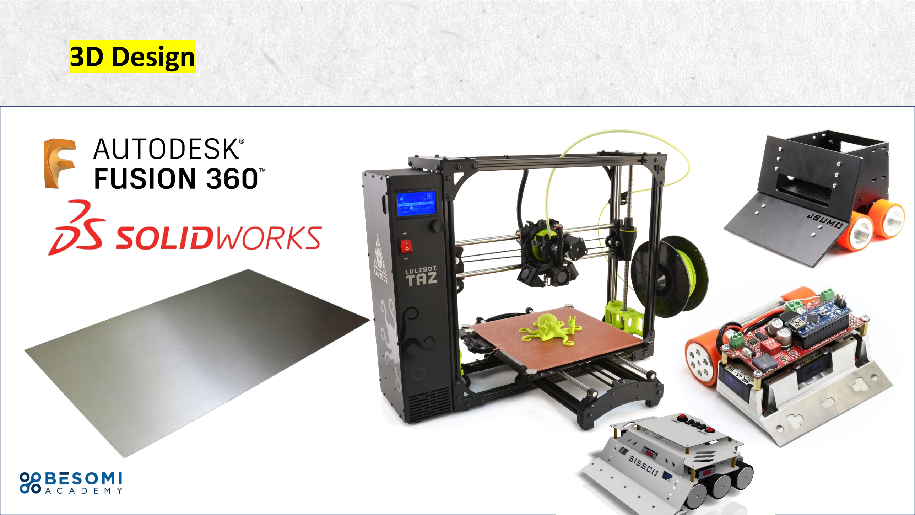
[picture p62: page 64]

## Fusion 360

Getting Started
To download and use Fusion 360, you will need an Autodesk ID. As a student or educator, you can obtain an Autodesk ID and Fusion 360 at www.autodesk.com/education/free-software/fusion-360

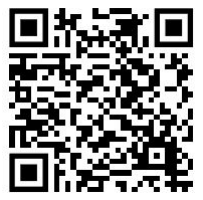
[picture p63: figure]

## Free to Use Designs

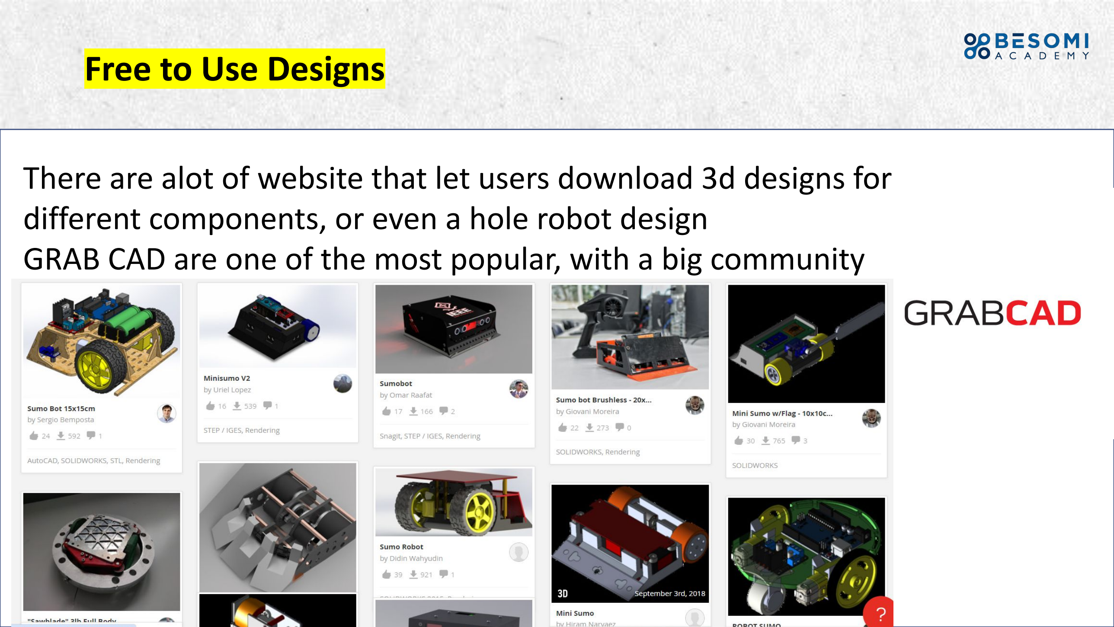
[picture p64: page 66]

### There are alot of website that let users download 3d designs for different components, or even a hole robot design GRAB CAD are one of the most popular, with a big community

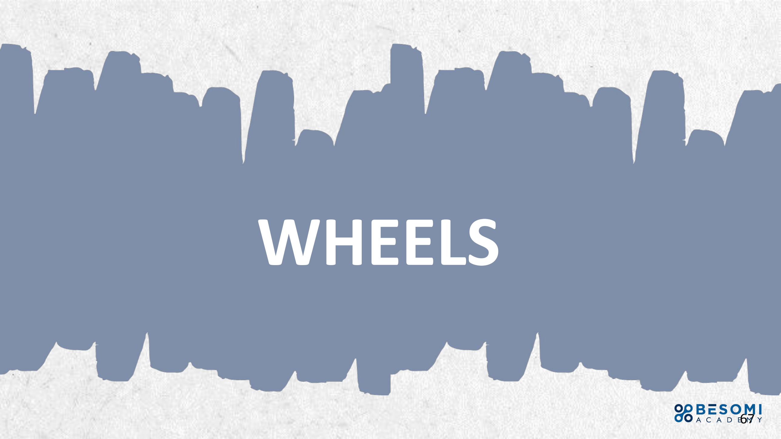
[picture p65: page 67]

67

# WHEELS

## Type of wheels

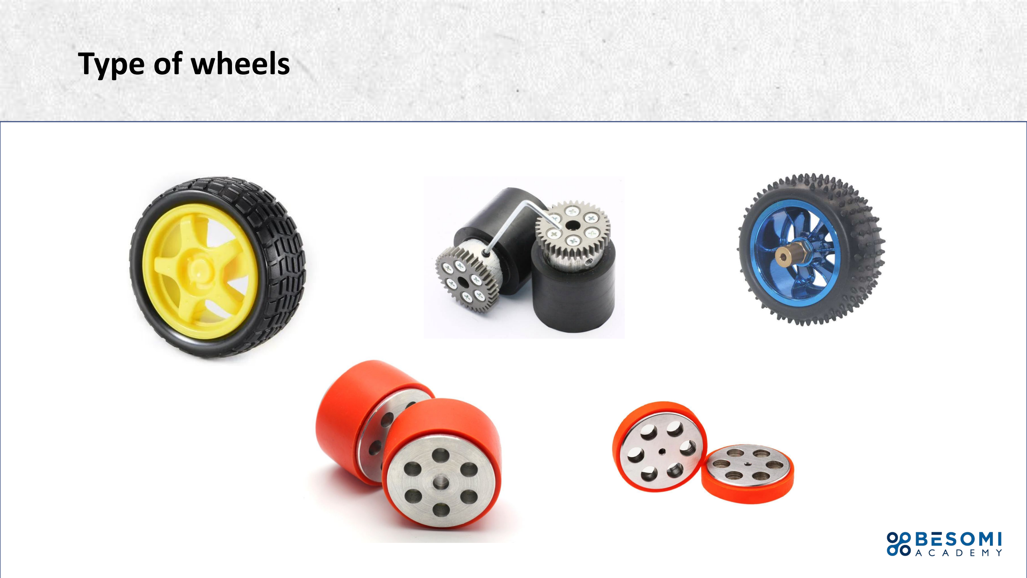
[picture p66: page 68]

## Wheel Diameter

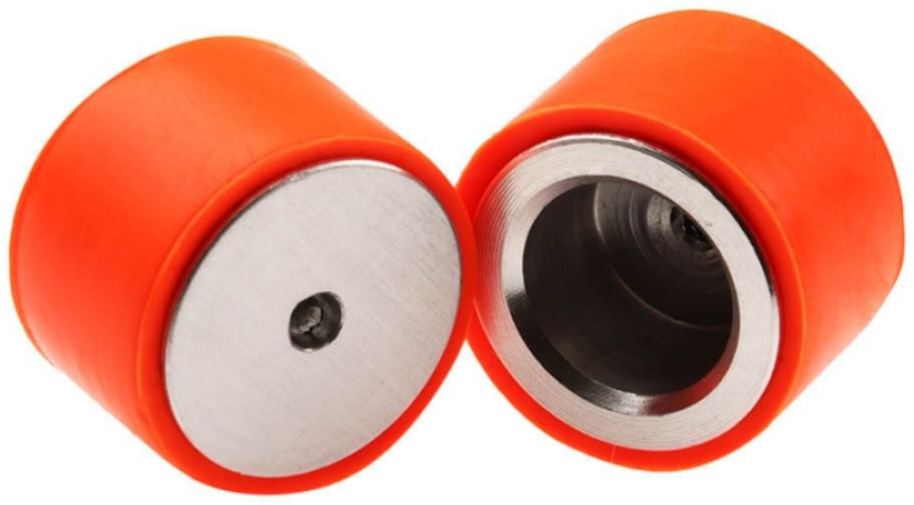
[picture p67: figure]

Small diameter:

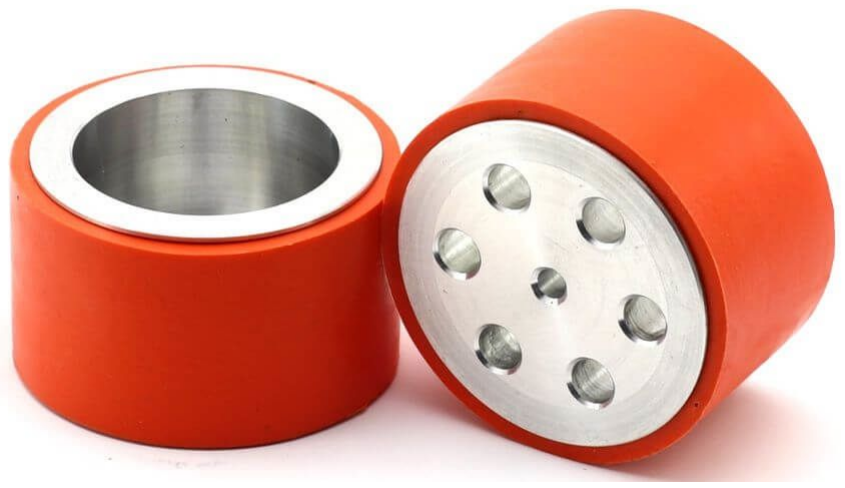
[picture p68: figure]

MORE TORQUE | Big diameter:
| MORE RPM

## Choosing the best wheels

### Which wheels are the best for my robot ?

## Wheel Diameter

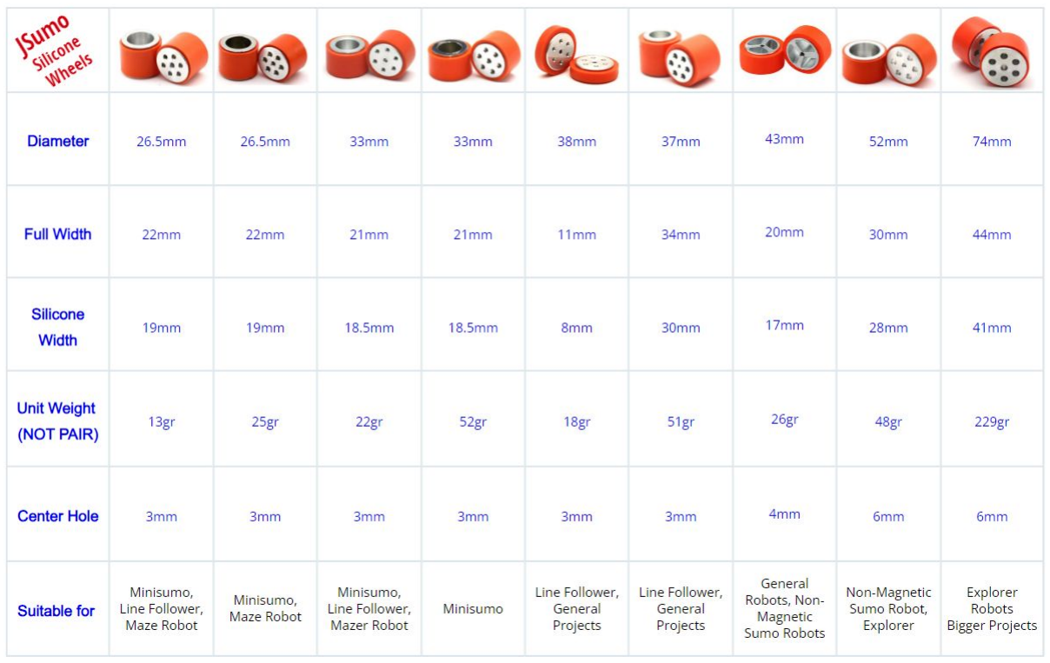
[picture p69: figure]

## Center Hole / Shaft size

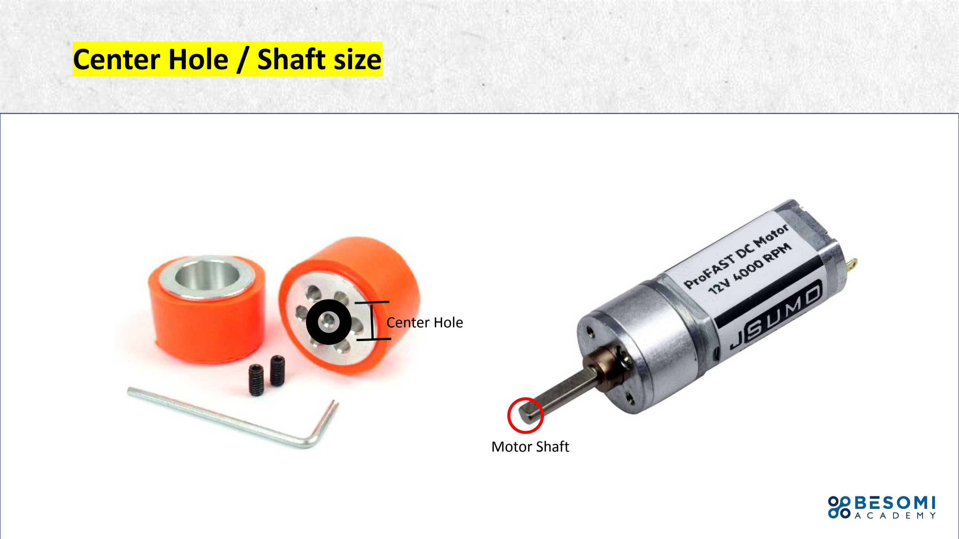
[picture p70: page 72]

Center Hole

Motor Shaft

## Easy Plug

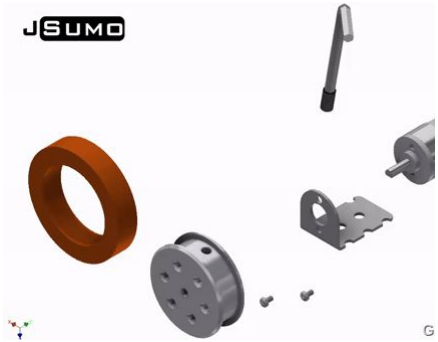
[picture p71: figure]
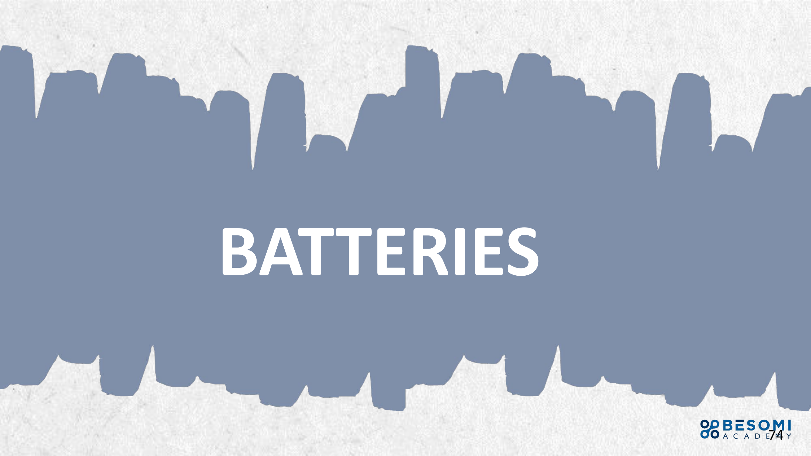
[picture p72: page 74]

74

# BATTERIES

## Battery Types

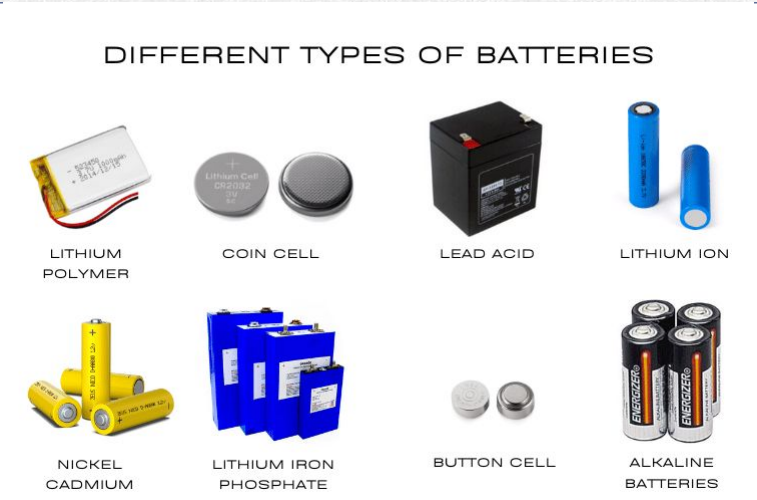
[picture p73: figure]

## What we use in our robots ?

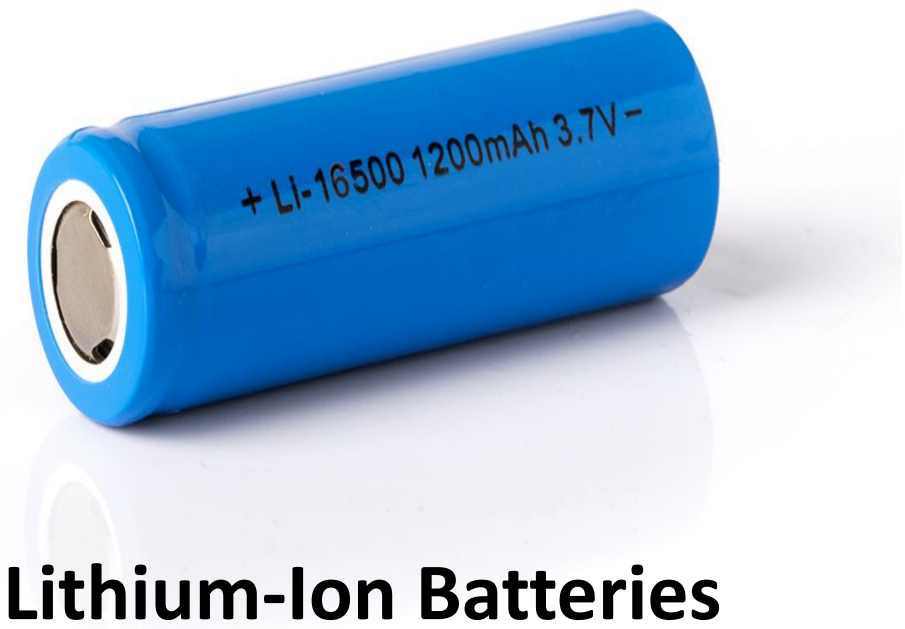
[picture p74: figure]
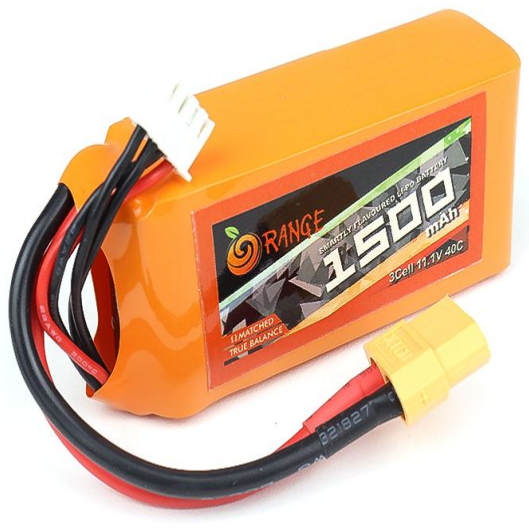
[picture p75: figure]

Lithium-Ion Batteries | Lithium Polymer

## POWER THE MOTORS

## Important things to look at when choosing your battery:

Voltage | + | Capacity

## POWER THE MOTORS

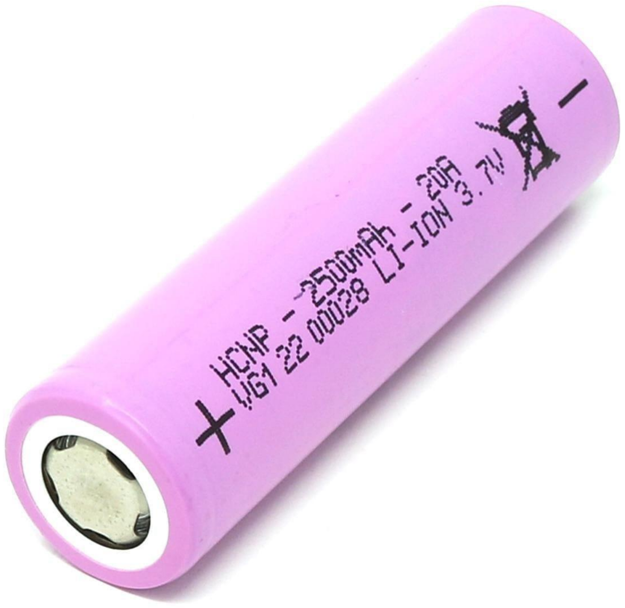
[picture p76: figure]

## POWER THE MOTORS

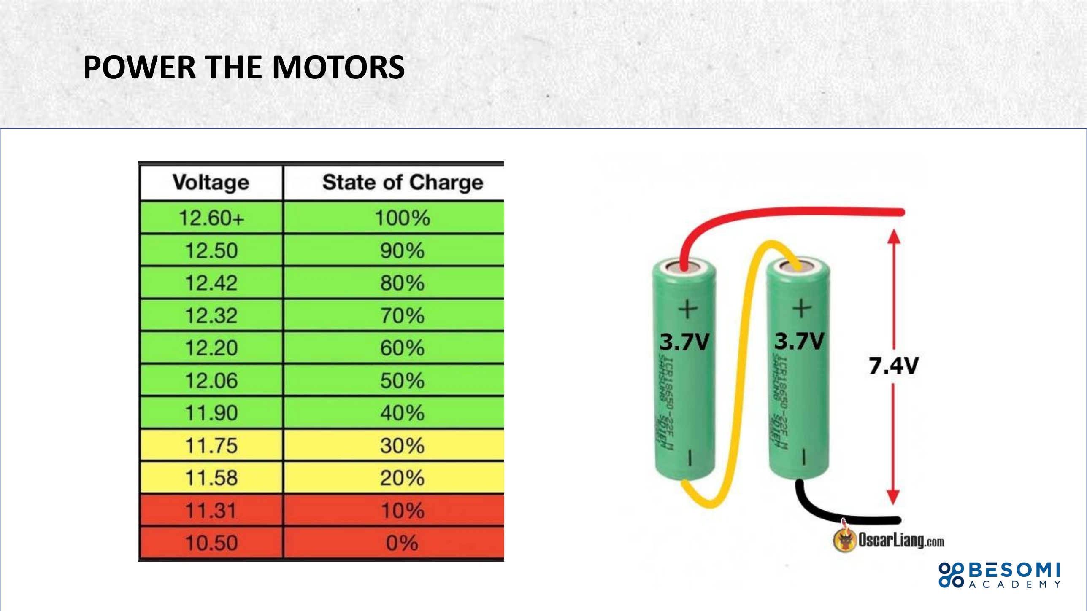
[picture p77: page 79]

## POWER THE MOTORS

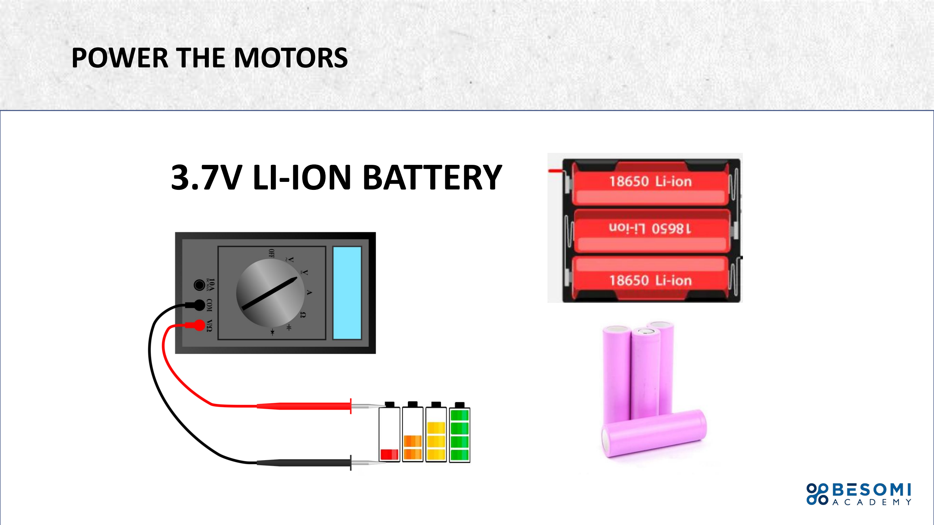
[picture p78: page 80]

## 3.7V LI-ION BATTERY

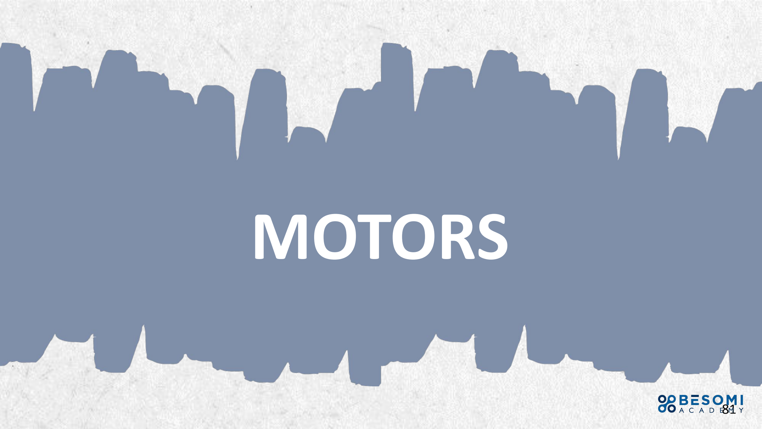
[picture p79: page 81]

81

# MOTORS

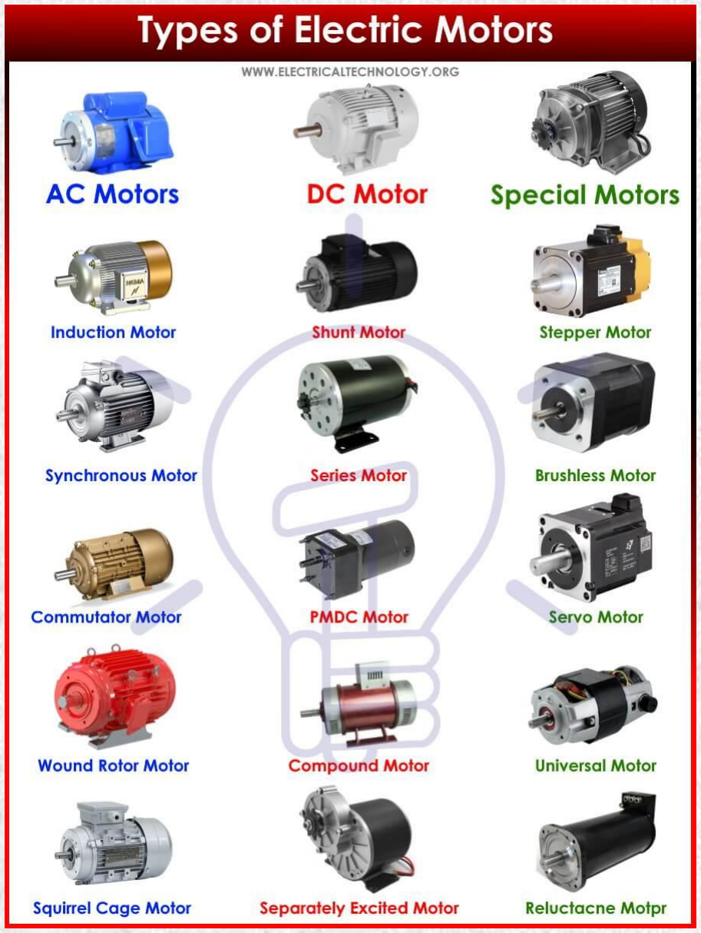
[picture p80: figure]
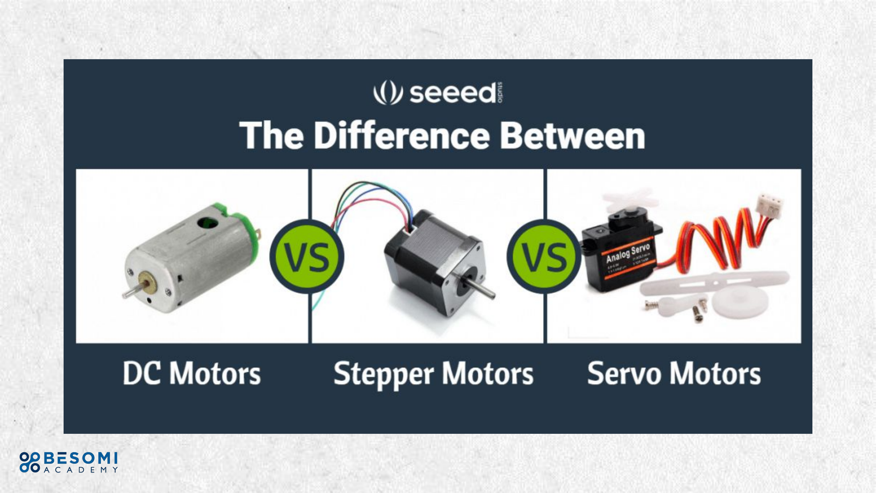
[picture p81: page 83]

## Motors for SUMO Robot

How to choose the best motor ?

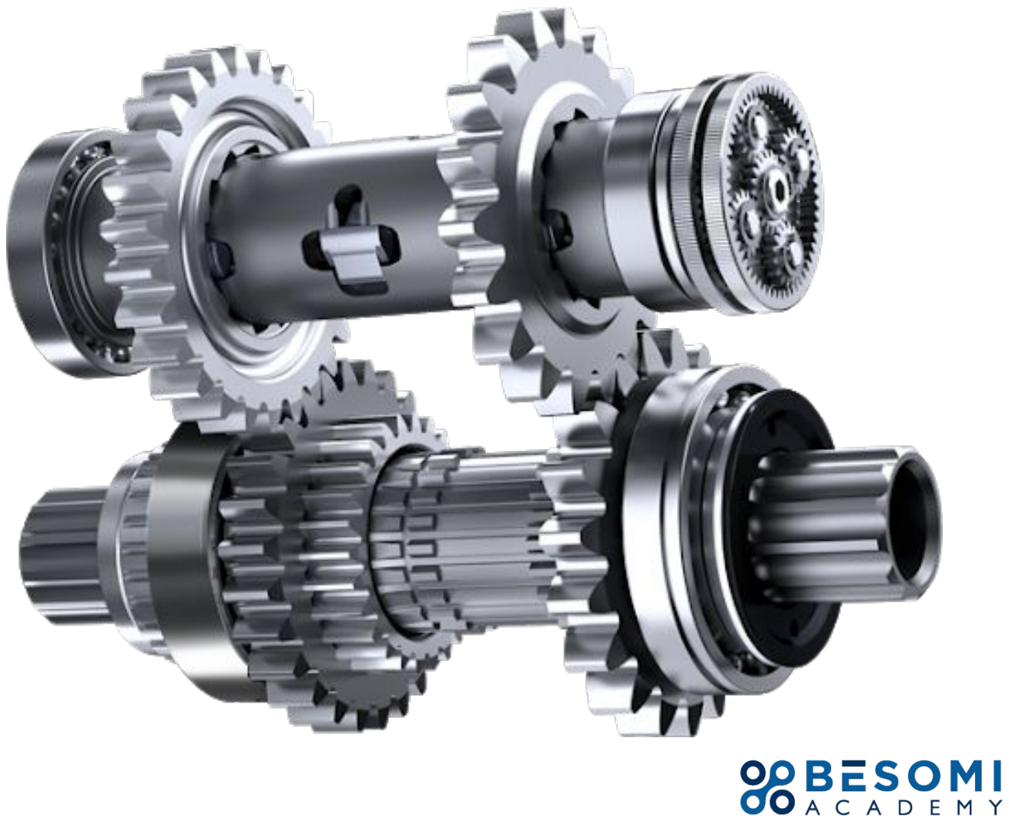
[picture p82: figure]

- Voltage Rating
- Stall Current
- RPM
- Torque

## Motors for SUMO Robot

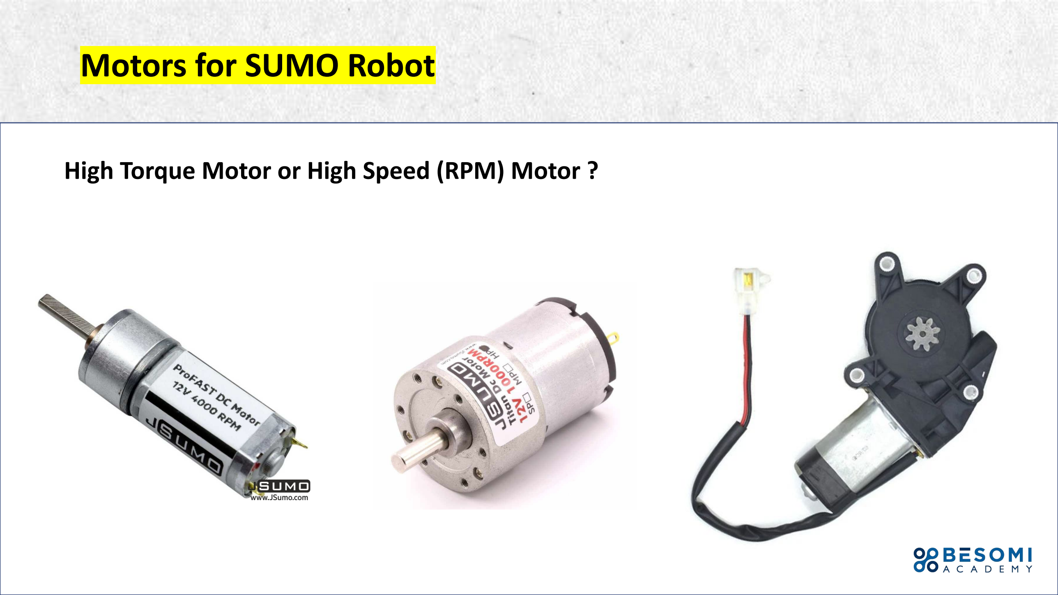
[picture p83: page 85]

High Torque Motor or High Speed (RPM) Motor ?

## Motors for SUMO Robot

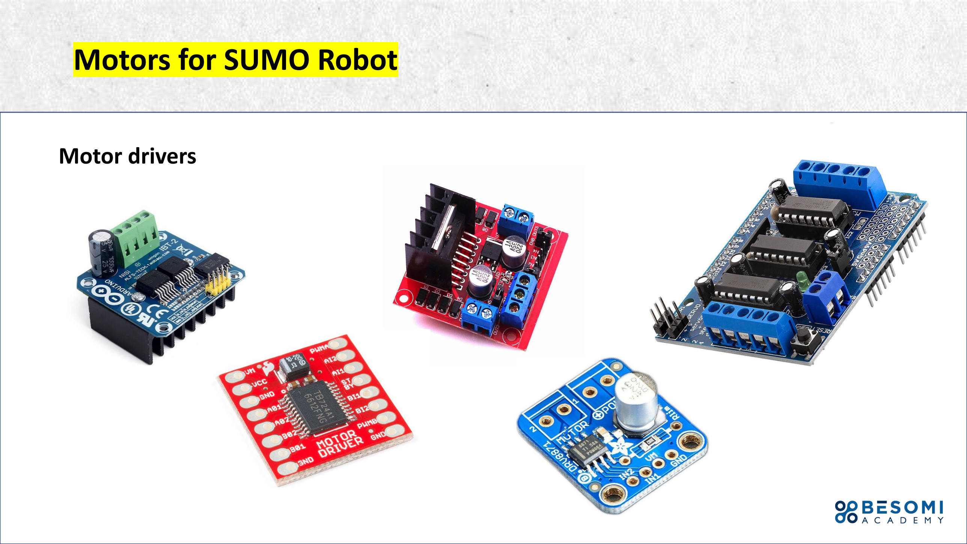
[picture p84: page 86]

Motor drivers

## Motors for SUMO Robot

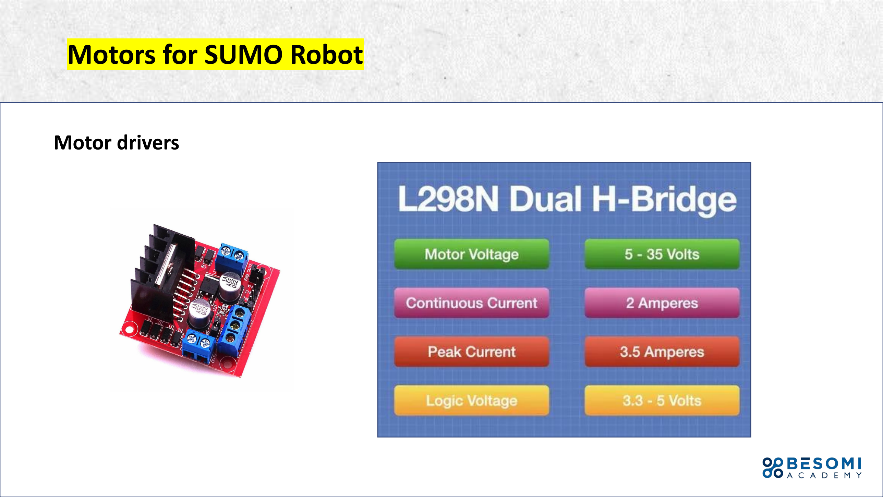
[picture p85: page 87]

Motor drivers

## Motors for SUMO Robot

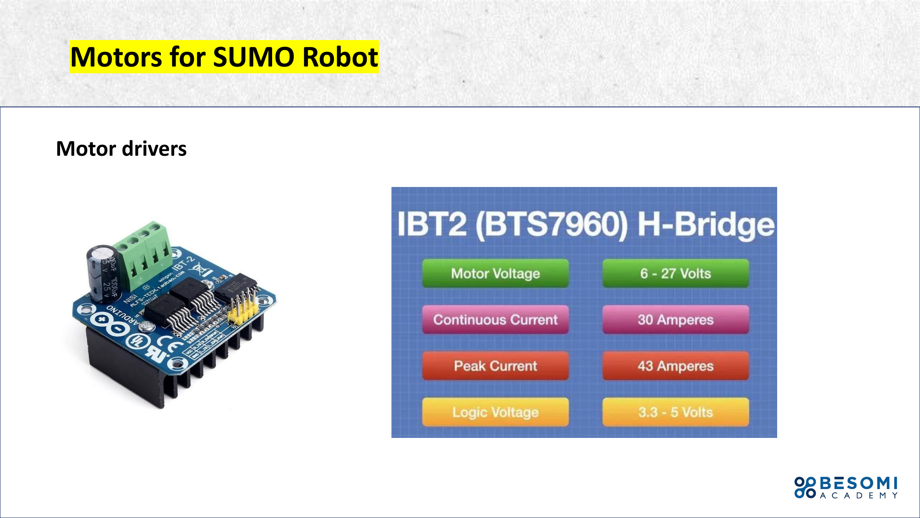
[picture p86: page 88]

Motor drivers

## Motors for SUMO Robot

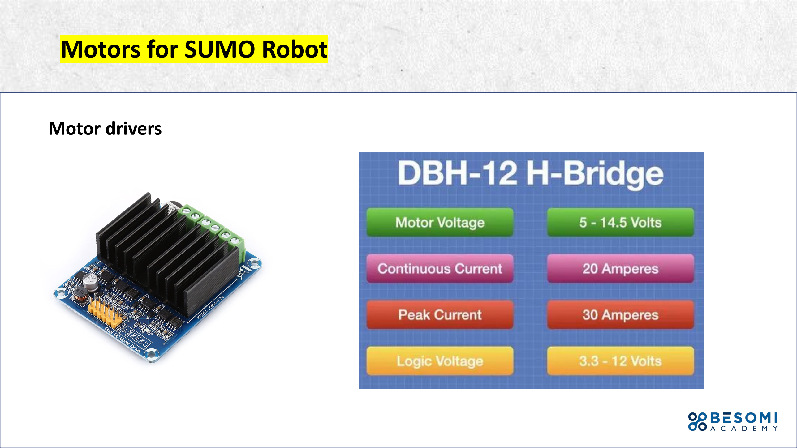
[picture p87: page 89]

Motor drivers

## BTS7960 MOTOR DRIVER WITH DC MOTOR

## Controlling a DC Motor

In order to have a complete control over DC motor, we have to control its speed and rotation direction. This can be achieved by combining these two techniques.

- PWM – For controlling speed
- H-Bridge – For controlling rotation direction

# makes life easier!!

## BTS7960 MOTOR DRIVER WITH DC MOTOR

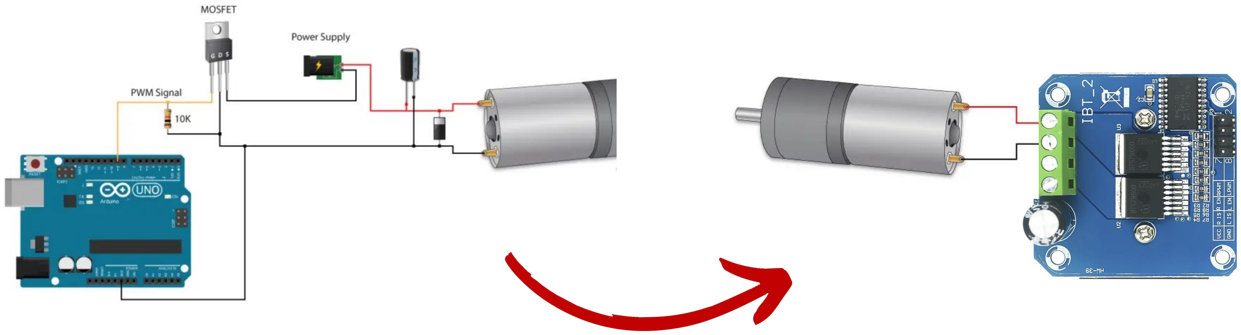
[picture p88: figure]

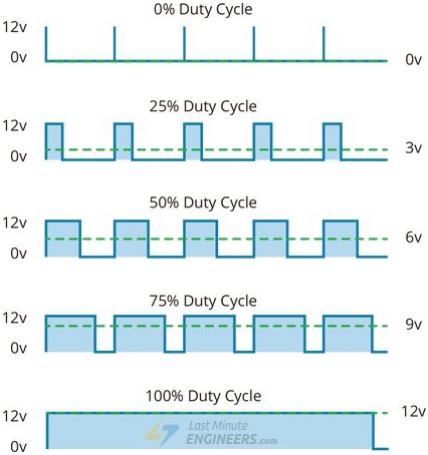
[picture p89: figure]

A) PWM – For controlling speed

The speed of a DC motor can be controlled by varying its input voltage. A common technique for doing this is to use PWM (Pulse Width Modulation).
PWM is a technique where average value of the input voltage is adjusted by sending a series of ON-OFF pulses.

## BTS7960 MOTOR DRIVER WITH DC MOTOR

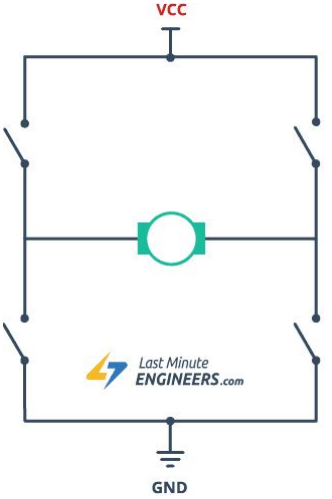
[picture p90: figure]

B) H-Bridge – For controlling rotation direction

The DC motor’s spinning direction can be controlled by changing polarity of its input voltage. A common technique for doing this is to use an H-Bridge.
An H-Bridge circuit contains four switches with the motor at the center forming an H-like arrangement.

## BTS7960 MOTOR DRIVER WITH DC MOTOR

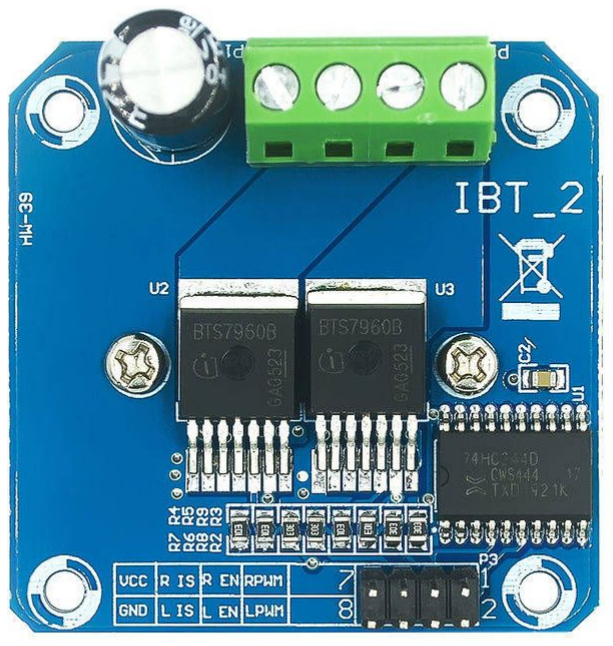
[picture p91: figure]

At the heart of the module is the big, black chip with chunky heat sink is an L298N.

## BTS7960 MOTOR DRIVER WITH DC MOTOR

## BTS7960 MOTOR DRIVER WITH DC MOTOR

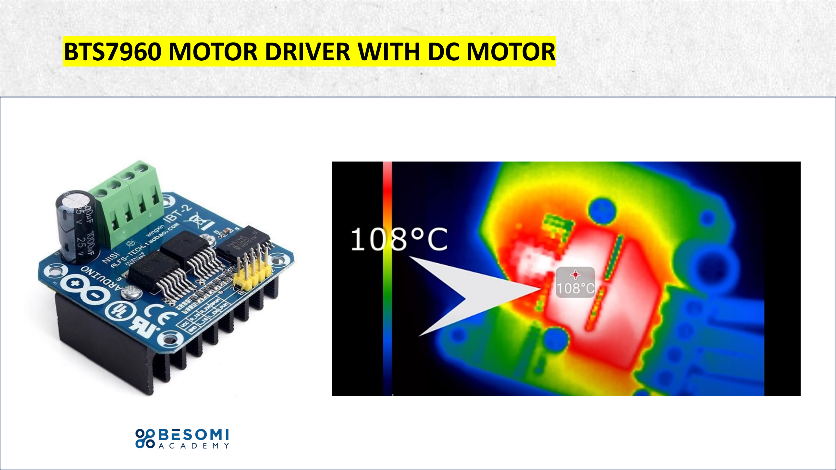
[picture p92: page 95]

## BTS7960 MOTOR DRIVER WITH DC MOTOR

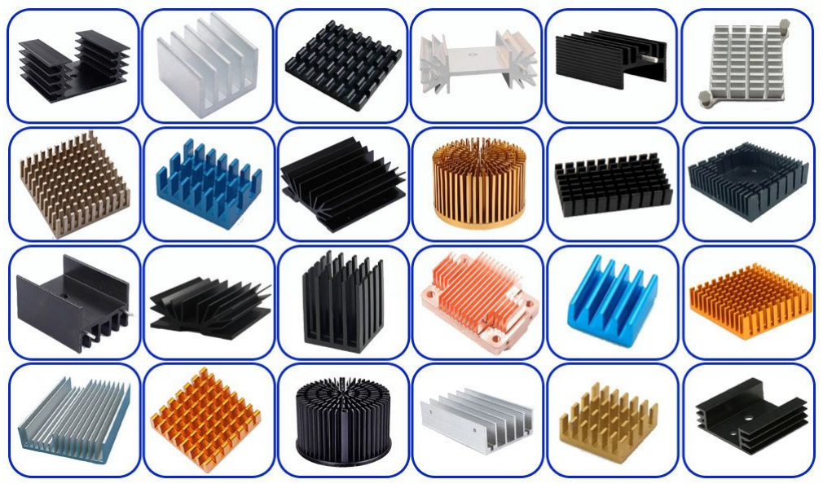
[picture p93: figure]

## BTS7960 MOTOR DRIVER WITH DC MOTOR

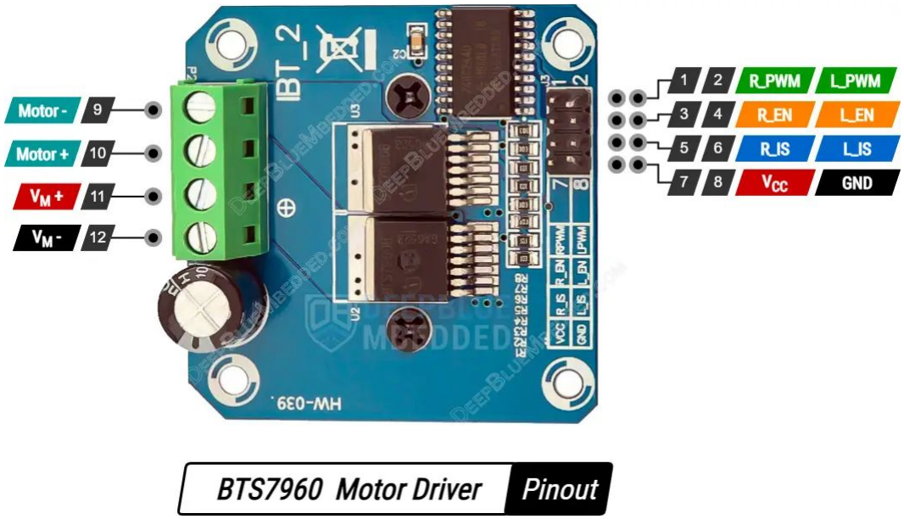
[picture p94: figure]

## BTS7960 MOTOR DRIVER WITH DC MOTOR

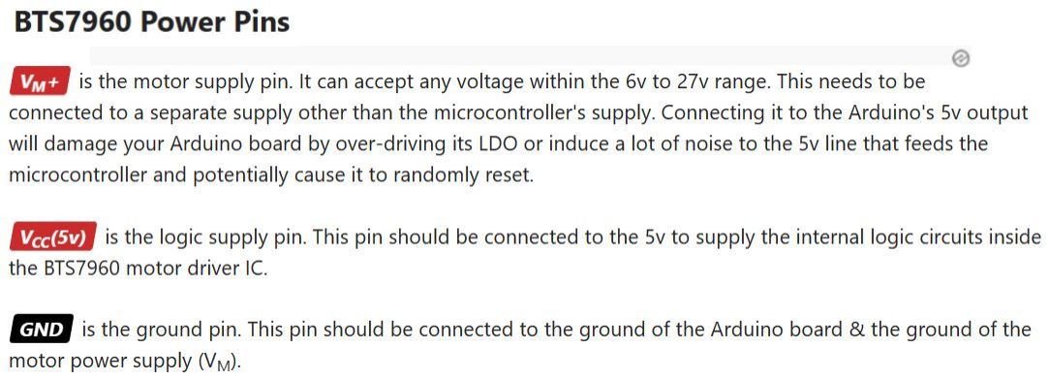
[picture p95: figure]

## BTS7960 MOTOR DRIVER WITH DC MOTOR

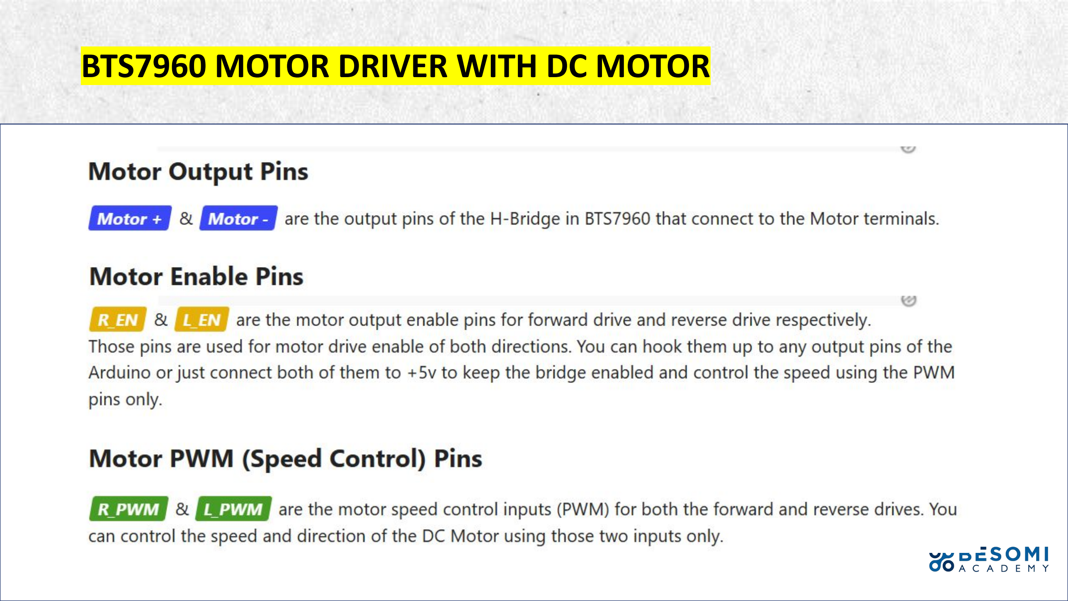
[picture p96: page 99]

## BTS7960 MOTOR DRIVER WITH DC MOTOR

## BTS7960 MOTOR DRIVER WITH DC MOTOR

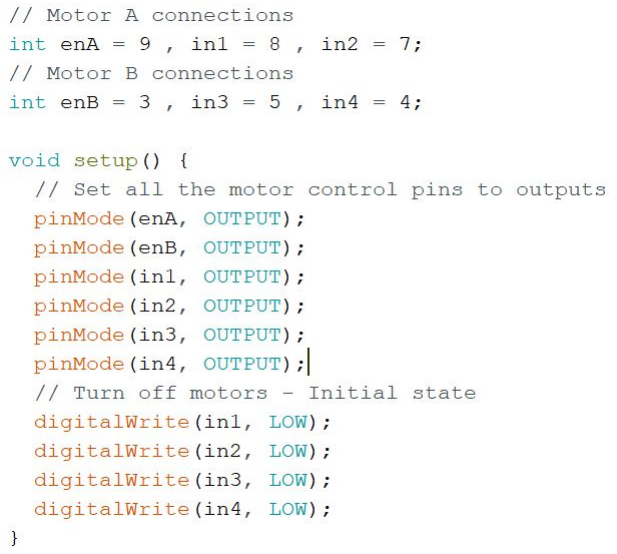
[picture p97: figure]
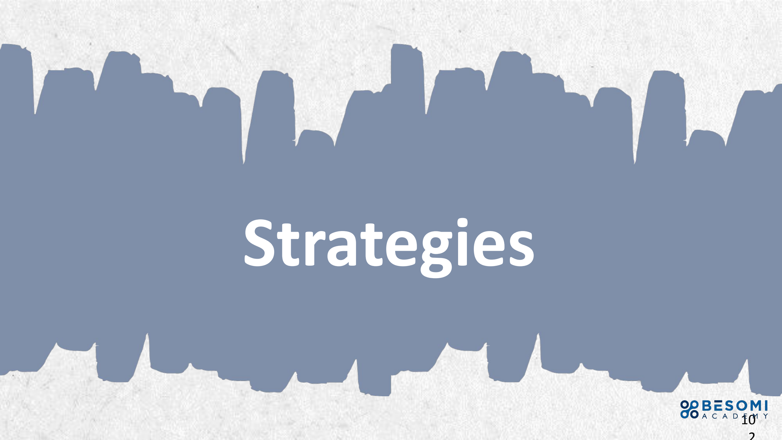
[picture p98: page 102]

10
2

# Strategies

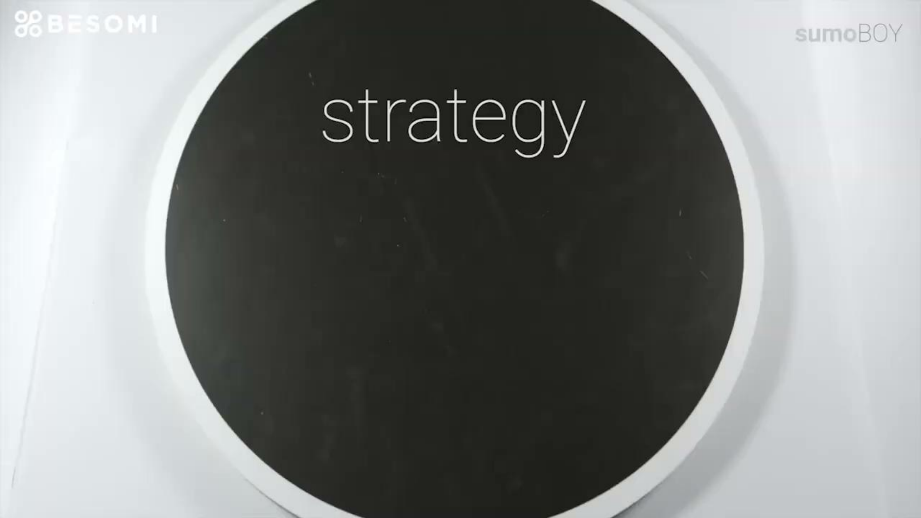
[picture p99: page 103]
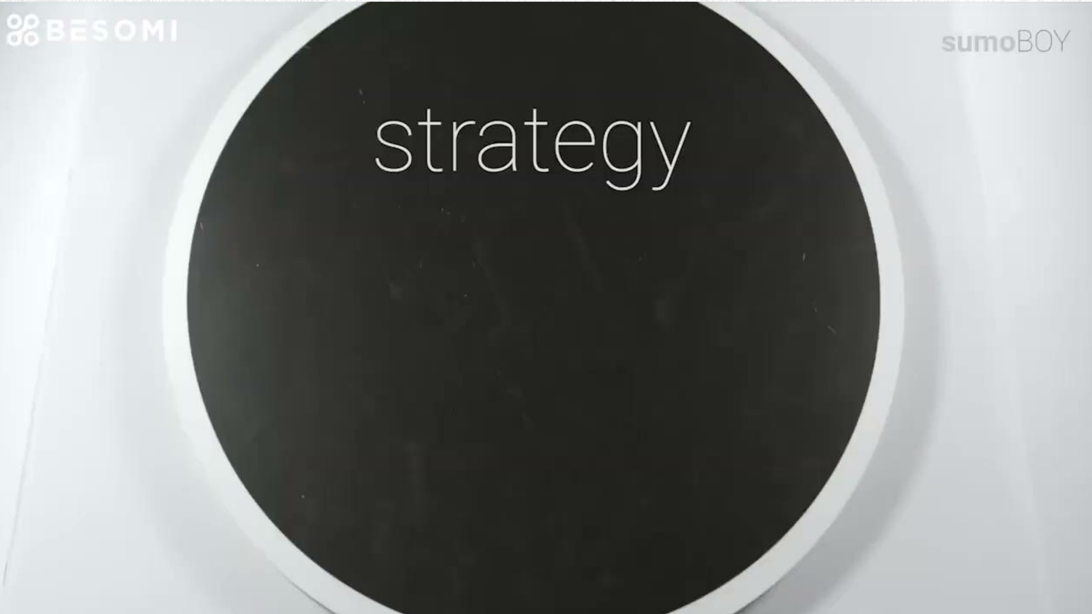
[picture p100: page 104]
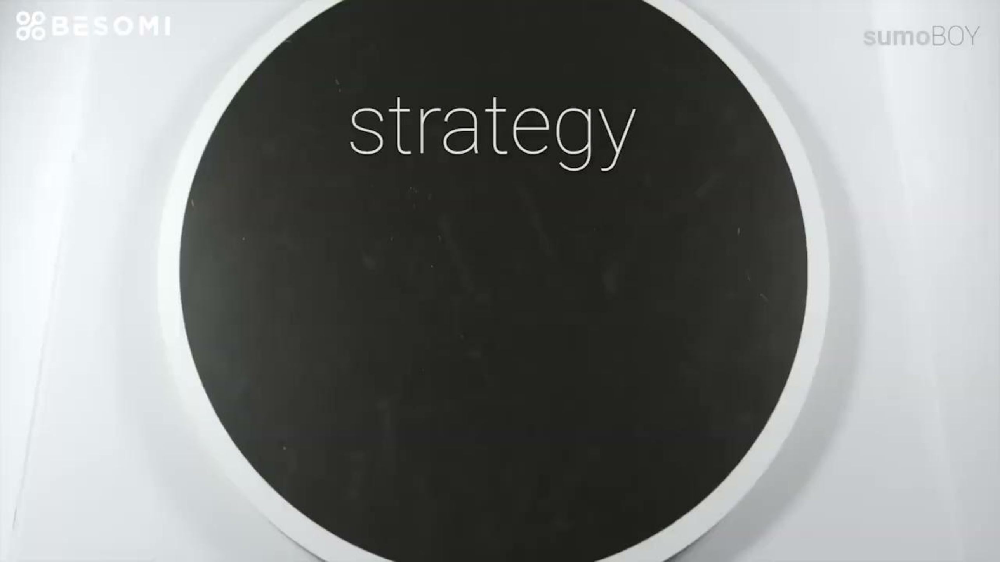
[picture p101: page 105]

## YOU ARE READY TO MAKE YOUR OWN SUMO ROBOT NOW

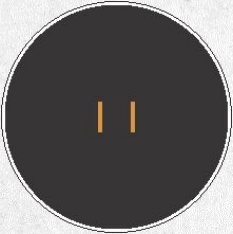
[picture p102: figure]

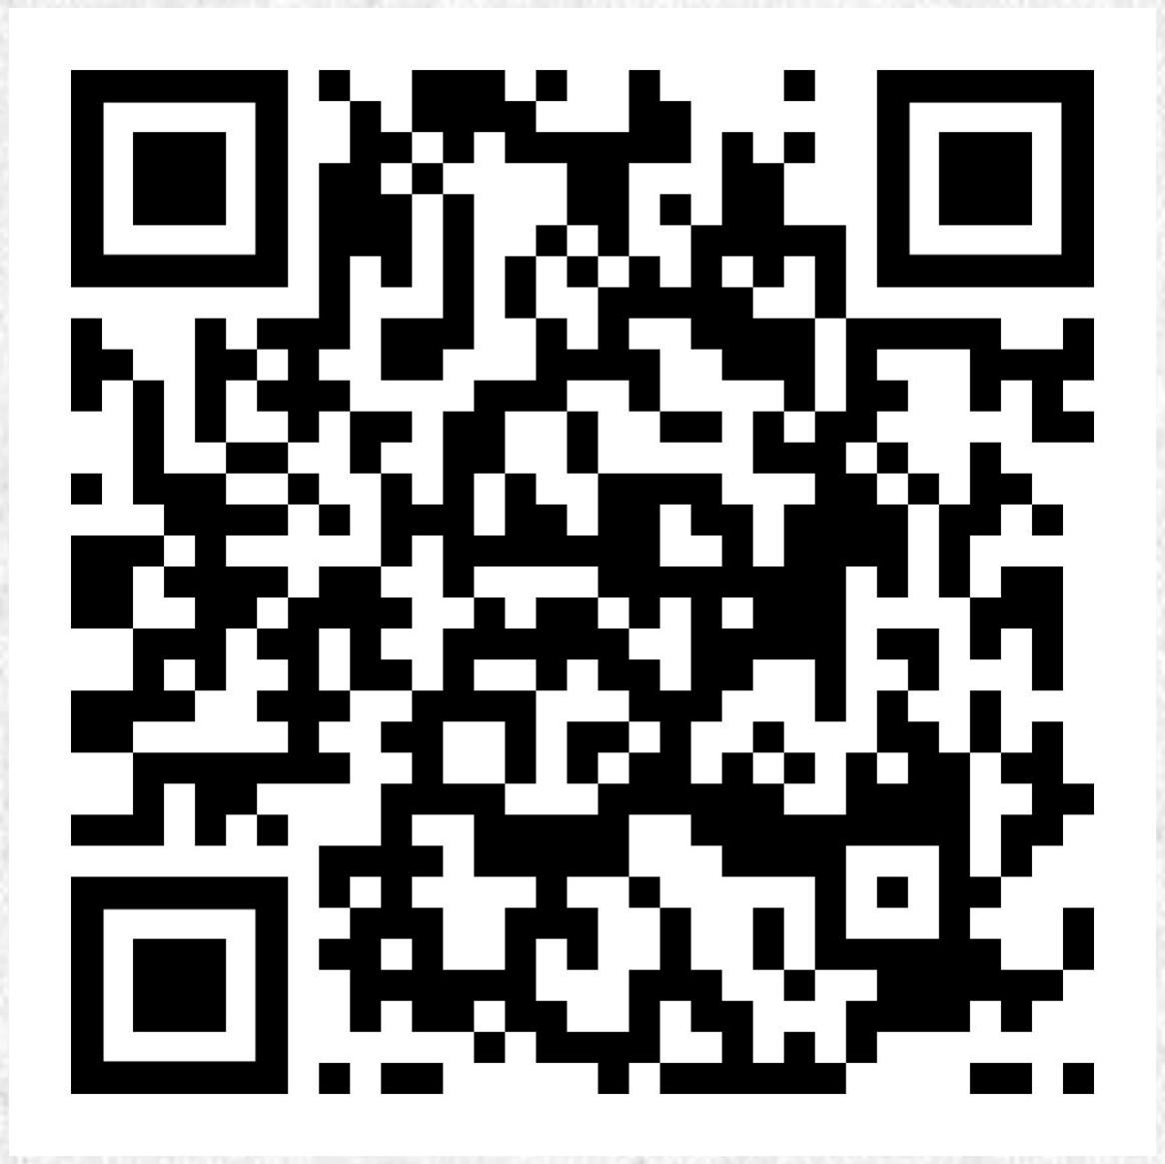
[picture p103: figure]

## RESOURCES

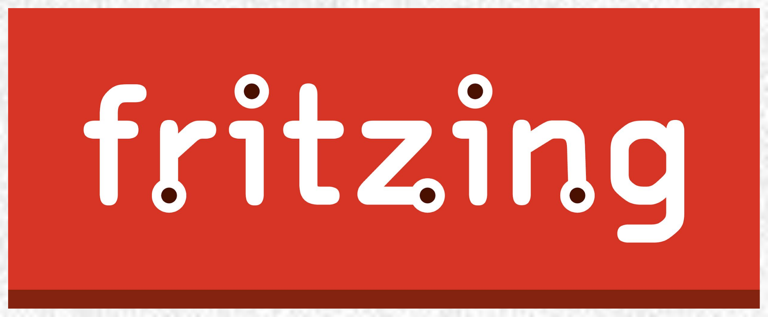
[picture p104: figure]
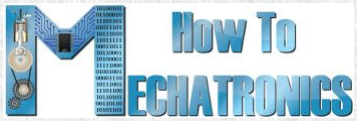
[picture p105: figure]

And many more resources either websites, communities or Youtube channels.

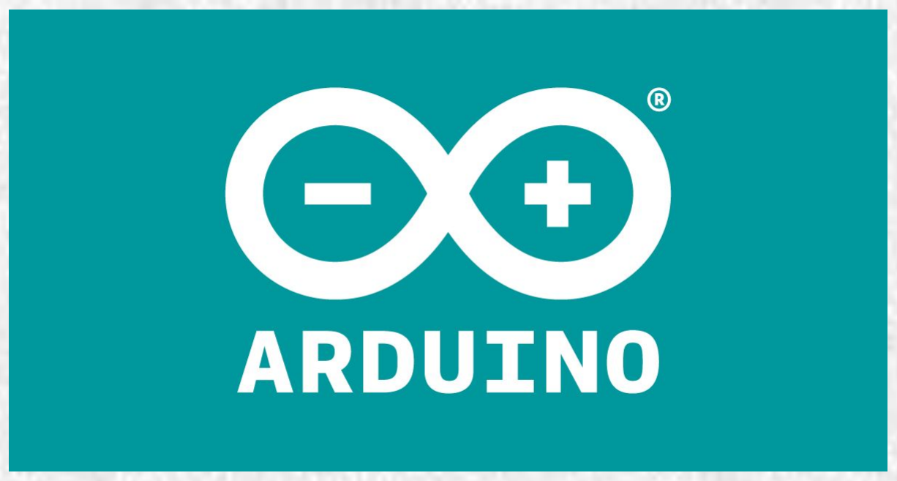
[picture p106: figure]

# “LEARNING HAS NO END”

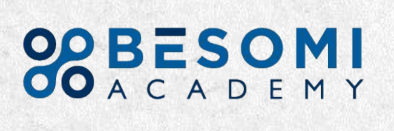
[picture p107: figure]
