Shreyankkkkk/foundations/certificates/README.md

# Certificates

Index of every certificate earned. PDFs are in the subfolder for their domain. Add a row whenever a new one is earned (newest at the bottom of each table).
File names: `issuer-credential.pdf`. Dates are blank where not yet confirmed; fill from the PDF.

## AI (`ai/`)
| Certificate | Issuer | Date | File |
|---|---|---|---|
| Claude 101 | Anthropic | | `ai/anthropic-claude-101.pdf` |
| Claude Code 101 | Anthropic | | `ai/anthropic-claude-code-101.pdf` |
| Claude Code in Action | Anthropic | | `ai/anthropic-claude-code-in-action.pdf` |

## Programming (`programming/`, `git-github/`)
| Certificate | Issuer | Date | File |
|---|---|---|---|
| Python Basics | FreeAcademy | | `programming/freeacademy-python-basics.pdf` |
| Python Basics | freeCodeCamp | | `programming/freecodecamp-python-basics.pdf` |
| Git and GitHub Mastery | FreeAcademy | | `git-github/freeacademy-git-and-github-mastery.pdf` |

## Robotics (`robotics/`)
| Certificate | Issuer | Date | File |
|---|---|---|---|
| Sumo Robot Workshop | Besomi | | `robotics/besomi-sumo-robot-workshop.pdf` |
| SumoX-26 competition | Dubai TechBots League | 2026-10-04 | `robotics/sumox-2026-competition.pdf` |

## General (`general/`)
| Certificate | Issuer | Date | File |
|---|---|---|---|
| Wired and Fired | EA | | `general/ea-wired-and-fired.pdf` |
