Shreyankkkkk/foundations/projects/amd-hackathon-act-iii/README.md

# AMD Hackathon ACT III

Hybrid AMD x lablab.ai hackathon, online build 2026-10-12 to 2026-10-18 (optional on-site phase in Italy): build a working business product, with a meaningful part running on AMD GPUs. Teams of 1 to 6. Prize pool $12,000+.

- Current status and rules: `STATE.md`
- Dated changes: `LOG.md`
- Digest of the brief: `docs/brief.md`
- Not to be confused with the AMD AI Academy Challenge (`projects/amd-hackathon/`).
