Shreyankkkkk/foundations/projects/amd-hackathon-act-iii/PORTABLE.md

# PORTABLE CONTEXT: amd-hackathon-act-iii
Generated 2026-10-10 by scripts/build_portable.py. Read-only copy; the source of truth is STATE.md / LOG.md in the repo.
Rule: if you cannot open a link below, say so and ask me to paste it. Never claim to have read what you could not open.
If you cannot write files, give me log lines and STATE edits as text to paste.

## Who
Shreyank, 2nd-year Mechatronics Engineering student (UOWD). Goal: quantitative finance (discretionary trading + systematic/quant development). This repo is a public log of everything he learns, builds and earns.

## Rules for AI
1. Read `AI-CONTEXT.md`, then `projects/<X>/STATE.md`. Open code files only when the task needs them. To find code, read `scripts/codemap/CODEMAP.md` first (auto-generated functions/classes per file with line numbers; trust names, line numbers may lag; outside the MCP open `https://raw.githubusercontent.com/Shreyankkkkk/foundations/main/scripts/codemap/CODEMAP.md`).
2. Constants: never invent or hard-code. Every constant gets its calculation or measurement shown beside it, plus the source. Unmeasured = say so, mark it `PLACEHOLDER`; assumed = `ASSUMED`.
3. Code changes: give the code and say which file and where in it the change goes (he does not know the file layout by heart).
4. Be token-efficient: no padding.
5. Never run git commit/push. Shreyank commits. Before big edits, remind him to commit first.
6. Use today's date for every log line; never guess a date. If a date is unknown, write `date?`.
7. Naming: lowercase kebab-case, no spaces, `exercises` (not excercises). Do not create empty folders. Every folder with real content gets a README.
8. Public repo: no passwords, tokens, ID numbers, personal finances or private chat content.
9. Tokens: never read a whole `LOG.md` or journal file; read the last 3 lines only (tail). To append a line, use `edit_file` with the last line as `oldText` and that line plus the new line as `newText`. Never rewrite a whole file with `write_file` when a few lines change. Log only when he says `log it`, not after every message. To find or read part of a file, use `search_code` and `read_lines` (foundations-helper MCP) instead of opening whole files; if they are not listed, use the filesystem tools.
10. Teaching notes: when he asks to learn a term or topic, reply with the note content only, in one code block, template: Definition / Why it matters (for the project) / How it works / Example / 3 self-test questions. Max 200 words per term, plain language first. He pastes it into the right file himself: do not create, edit or re-read note files unless asked. Project notes go in `projects/<slug>/notes/`; reusable ones in `learning/<area>/notes/`.
11. If you cannot open a file or link, say so and ask him to paste it. Never claim to have read something you could not open. Outside the MCP, open raw file URLs (`raw.githubusercontent.com/...`), not GitHub directory pages.
12. `STATE.md` stays under about 150 lines and holds current truth only; history belongs in `LOG.md`. `projects/*/PORTABLE.md` is generated by `scripts/build_portable.py`: never edit it by hand.

## How to log (three layers, end of every session)
1. `journal/YYYY-MM.md`: append one line per session: `YYYY-MM-DD | learn/build/plan/research/achieve | what | files`.
2. Project work only: also append the detailed line to that project's `LOG.md`: `YYYY-MM-DD | what changed | why | evidence (file path or commit)`.
3. If the project's truth changed (a constant, a decision, a status): update its `STATE.md`. If a certificate was earned: add a row to `certificates/README.md`.
Newest at the bottom. One line per entry, however small. List changed files in the reply.

---

## STATE (amd-hackathon-act-iii)

# AMD Hackathon ACT III STATE

AMD Developer Hackathon: ACT III (lablab.ai x AMD). Hybrid: online build 2026-10-12 to 2026-10-18, optional on-site 10-17/18 in Italy (travel not covered).
Status: day 0, pre-kickoff. AMD sign-up done (new account). lablab "Enroll" and Discord join: unconfirmed.
Goal: priority 1 = experience and learning; priority 2 = winning. Team: decided 2026-10-09 meeting; 6 members (2 backend incl. Shreyank, 2 frontend, 1 marketing, 1 repo), which is the maximum allowed. Roles in Decisions.
Idea (initial, from team meeting): "Google Earth for the inside of a building". Owner sends static images; AI converts them into a 3D simulation to walk through remotely. Uses named: hotels; factories where machinery is dangerous so students can view remotely. Not validated, see Risks.
Note: the earlier Dec 1 date belonged to a different event (AMD AI Academy Challenge, see `projects/amd-hackathon/`). It does not apply here.

## Rules and constraints (rule | value | source)
| Rule | Value | Source |
|---|---|---|
| Registration | Closes at kickoff: 2026-10-12 15:00 UTC; approval needs AMD AI Developer Program membership plus lablab enrollment and Discord | live page, event page |
| Submission deadline | 2026-10-18 15:00 UTC; judging starts then | live page |
| Team size | 1 to 6; teammates findable on dashboard or Discord | event page |
| Challenge | Pick one of 4 business tracks (Intelligent Industry, Health and Wellbeing, Reinvent Commerce, Create a New Kind of Experience), or the Evolus partner track | event page |
| AMD requirement | A meaningful part of the workload must run on AMD (Developer Cloud, Instinct, ROCm, Ryzen AI, Radeon) AND be part of the working product shown to judges | event page |
| Models and tools | Own choice of compatible models, frameworks and tools | event page |
| Submit | Title, short and long description, track, tech tags, cover image, demo video, slide deck, public GitHub repo, demo platform, application URL, working prototype | event page |
| Judging | Application of Technology, Presentation, Business Value, Originality | event page |
| Track 3 rule | Do not use an LLM as the only forecasting method; explain how predictions are calculated | event page |
| Track 2 rule | No autonomous diagnosis or treatment advice; show uncertainty, human review, handling of sensitive data | event page |
| Track 4 rule | Show the experience changing for at least 2 audiences or inputs; state cost per experience and who pays | event page |
| Evolus track | Free Evolus workspace via event code shared at kickoff (valid to 2026-10-31, up to 6 members, 50,000 credits); main agent must use an open model on own vLLM endpoint on AMD Developer Cloud; at least 2 Evolus building blocks; drive Evolus through its APIs; containerized app, public repo, runnable README | event page |
| Vibe Generation special prize | AirPods 5 for each member of the best solution; judged on Hybrid, Becreatives, Vibe Generation | event page |
| Prize pool | $12,000+; split per track not shown on the page | event page |
| Credits | $100 AMD Developer Cloud credits for new ADP members | event page |
| Originality and licence | Submissions must be original and MIT-compliant | event page |
| Prize payout | Up to 90 days | event page |
| Secrets | Never commit API keys; use environment variables | event page (Evolus track) |
| Submission limits | Title clear and descriptive (max 50 chars per guidelines article); short description max 255 chars; long description min 100 words covering problem, solution, audience, unique features; tags; cover image PNG/JPG 16:9; video MP4 max 5 min (under 300 MB per guidelines article); slides PDF; public GitHub repo; demo platform; application URL | rule book, submission guide, guidelines article |
| Demo platform | Rule book names Streamlit, Replit or Vercel. Evolus track needs a containerized app. Which hosts are accepted for a GPU-backed app is not stated | rule book, event page; UNVERIFIED |
| Repo visibility | Private repo means judges cannot fully review; lower score. Judges check the repo; commits spread across the event window are a stated positive signal (lablab guide, not a rule) | submission guide, how-to-win guide |
| Late submission | Manual submission only for 6 h after the deadline, only with a valid reason and prior approval from organizers or mentors | rule book |
| Conduct | Plagiarism, gaming voting, unauthorized automation, tampering or fraud: removal or disqualification. Not following submission guidelines: lower score or exclusion | rule book |
| IBM Bob report | Submission guide asks for an exported IBM Bob report. Not mentioned on the ACT III event page, so likely carried over from another event; check the getting-started guide | submission guide; UNVERIFIED for ACT III |
| Team approval | Each member needs AMD AI Developer Program membership + lablab enrollment + Discord before kickoff; assumed per person, UNVERIFIED | event page |
| Not covered by the rule book | Eligibility (age, country), what may be prepared before kickoff, AI-assisted coding, third-party code and data, licensing detail beyond MIT. Getting-started guide still unread | rule book; open |

## Constants (name | value | calculation | source | status)
| Name | Value | Calculation | Source | Status |
|---|---|---|---|---|
| days_to_kickoff | 3 | 2026-10-12 minus 2026-10-09 (was 4 on 2026-10-08) | calendar | DERIVED |
| kickoff_gst | 19:00 GST on 2026-10-12 | 15:00 UTC + 4 h (GST = UTC+4) | live page | DERIVED |
| submission_close_gst | 19:00 GST on 2026-10-18 | 15:00 UTC + 4 h | live page | DERIVED |
| build_window_h | 144 h | 6 days x 24 h (kickoff to submission close) | live page | DERIVED (calendar hours, not working hours) |
| manual_submission_close_gst | 01:00 GST on 2026-10-19 | 15:00 UTC on 10-18 + 6 h = 21:00 UTC; + 4 h GST | rule book, live page | DERIVED (needs prior approval; not a plan) |
| registered_2026-10-08 | 5,007 | read from live page | live dashboard | MEASURED |
| teams_forming_2026-10-08 | 871 | read from live page | live dashboard | MEASURED |
| hours_available | ? | ask Shreyank (uni schedule) | - | PLACEHOLDER |
| time_split | 20% research / 60% build / 20% demo, README, submission, of hours_available | WORKFLOW.md rule of thumb | WORKFLOW.md | ASSUMED until hours_available is known |
| freeze_date | date? | set once hours_available and track are known | - | PLACEHOLDER |
| credit_cost_per_gpu_hour | ? | measure on AMD Developer Cloud | - | PLACEHOLDER |
| credit_hours_total | ? | $100 divided by credit_cost_per_gpu_hour | page, measurement | PLACEHOLDER |

## Decisions (choice | reason | rejected | status)
| Choice | Reason | Rejected | Status |
|---|---|---|---|
| Enroll before kickoff | Registration closes at 2026-10-12 15:00 UTC | Enrolling late | Recommended, pending Shreyank |
| Team vs solo | Team (decided at team meeting, 2026-10-09 report by Shreyank) | Solo | DECIDED |
| Idea | Indoor 3D walkthrough generated by AI from owner-supplied static images; hotels and factory training as use cases | - | INITIAL, not validated |
| Roles | 6 members. Backend: Shreyank + 1 teammate. Frontend: 2 teammates. Marketing: 1 teammate (contact other teams, sponsors). Repo: 1 teammate sets up the repo, all are contributors, work comes as pull requests he reviews and merges. Corrected 2026-10-10: marketing is a separate person, not one of the frontend two | - | AGREED, stated by Shreyank |
| Track | Not chosen. Idea fits Create a New Kind of Experience (needs 2 audiences/inputs and cost per experience) or Intelligent Industry (factory case needs realistic industrial data and an alert/action). Event page says "one or more tracks" but submit form says "Selected challenge"; plan for one until answered (primary-research F1/U4) | - | OPEN |

## Open items / next actions
1. Confirm lablab enrollment and Discord join (deadline above). Shreyank.
2. Answer the remaining setup questions (hours per day per member, online only); fills `hours_available`. Team is decided.
3. Read the getting-started guide in a browser (fetcher cannot render lablab guide pages reliably); settle the "Not covered by the rule book" row.
4. Check whether ACT III counts toward AI Academy XP (see `projects/amd-hackathon/`).
5. Primary research queue (checklist done 2026-10-09 in `docs/primary-research.md`: findings F1-F12, unknowns U1-U12, constants C1-C9; measurements and answers still pending): AMD Developer Cloud GPU type, $/h, credit hours, vLLM serve test; Docker/Linux on Shreyank's machine; schedule and mentor hours in GST; track requirements vs skills.
6. Secondary research queue (not started): past lablab/AMD winners in tracks of interest, vLLM-on-ROCm docs, Evolus quickstart, track datasets. Tag each finding SOURCED or RECALLED.
7. No code until primary research is logged here.
8. Idea validation (primary research, not started): what input quality the image-to-3D step needs (single photos vs many overlapping photos), whether it runs on AMD GPU and at what time/cost per building, existing indoor-tour products to compare against.

## Risks (idea) (all ASSUMED until researched)
- Turning a few static images into a believable 3D space is hard; single images give invented geometry. Demo must not claim measured accuracy it cannot show. RECALLED, verify.
- AMD must be a real part of the shown product (prize gate): the generation step is the natural place; needs a vLLM/ROCm or equivalent path tested on Developer Cloud.
- Existing indoor 3D tour products exist; originality has to come from the image-to-simulation step and the factory training use case.
- One reviewer merging all pull requests is a bottleneck during a 144 h window; agree review turnaround.

## Where things are
- `docs/brief.md`: complete brief (event, tracks, rules, submission, judging, discrepancies, sources)
- `docs/primary-research.md`: primary research checklist (findings, unknowns U1-U12 with where to find them, constants C1-C9 to measure, judge view, track fit)
- `LOG.md`: dated changes

---

## LOG (last 10 entries)

2026-10-08 | project created; event page and live page read and digested | the first link (AMD AI Academy Challenge) was the wrong event, so this is the real project | STATE.md, docs/brief.md
2026-10-08 | docs/brief.md written; guidelines article read; submission limits and team-approval rows added to STATE.md; rule book flagged unreadable by fetcher | files existed without brief.md; open items needed sources | STATE.md, docs/brief.md
2026-10-08 | rule book and lablab guides (pasted by Shreyank) folded in: brief.md rewritten as the complete brief; STATE.md gained demo-platform, repo, late-submission, conduct, IBM Bob and rule-book-gap rows, manual_submission_close_gst, research queues | initial setup completed; research not started | docs/brief.md, STATE.md
2026-10-08 | ERROR: a parallel session's complete docs/brief.md was overwritten with the reduced first version; warning added at its top; duplicate projects/README.md row removed | two sessions wrote to this folder without read-before-write | docs/brief.md, projects/README.md
2026-10-09 | primary research checklist written (12 findings, 12 unknowns, 9 constants to measure, judge view, track fit); STATE updated: days_to_kickoff 3, track-count conflict noted, research pointer | event page re-read; brief.md left unchanged by request; getting-started guide unreadable by fetcher, still needed | docs/primary-research.md, STATE.md
2026-10-09 | team decided after team meeting (reported by Shreyank); initial idea: AI-generated 3D indoor walkthrough from owner images (hotels, factory training); roles and PR workflow recorded; risks and idea-validation item added; track still open | team meeting outcome, not yet validated against rules or AMD hardware | STATE.md
2026-10-10 | team composition corrected: 6 members (2 backend, 2 frontend, 1 marketing, 1 repo), not 5; Roles and Team line in STATE updated | Shreyank clarified; logged only, discussion continues in the main ACT III chat | STATE.md

---

## Other files (open only if the task needs them)

- https://raw.githubusercontent.com/Shreyankkkkk/quant-foundations/main/projects/amd-hackathon-act-iii/docs/brief.md
- https://raw.githubusercontent.com/Shreyankkkkk/quant-foundations/main/projects/amd-hackathon-act-iii/docs/notes_1.md
- https://raw.githubusercontent.com/Shreyankkkkk/quant-foundations/main/projects/amd-hackathon-act-iii/docs/Opportunity_Research_Report.md
- https://raw.githubusercontent.com/Shreyankkkkk/quant-foundations/main/projects/amd-hackathon-act-iii/docs/primary-research.md
