Shreyankkkkk/foundations/projects/monte-carlo-simulation/LOG.md

# Monte Carlo Simulation LOG

Format: `date | what changed | why | evidence`. Newest at the bottom.

2026-10-04 | STATE.md and LOG.md created | start of MCP-based logging | projects/monte-carlo-simulation/STATE.md
2026-10-06 | renamed folders: `ai-refactored-monte-carlo` to `current`, `monte-carlo-simulation-shreyank` to `archive`; repo-wide lowercase restructure (`Projects/` is now `projects/`) | shorter names, matches project convention | projects/monte-carlo-simulation/STATE.md

TODO: backfill the version history (v1.0.0 to v6.2.0, AI refactor) from old chats and git history (`git log -- projects/monte-carlo-simulation Projects/monte-carlo-simulation`).
