Shreyankkkkk/foundations/projects/amd-hackathon-act-iii/docs/brief.md

# Brief digest

> WARNING 2026-10-08: this is the REDUCED first version (event page and live page only). A fuller brief that folded in the rule book and lablab guides was overwritten by mistake. The rule-book facts survive as rows in `STATE.md`. Rebuild the full brief from the rule book and guides before relying on this file; the "NOT yet read" line below is out of date.

Read 2026-10-08. Paraphrased, not copied. Tag: SOURCED = read directly from the source.

## Sources
- Event page: https://lablab.ai/ai-hackathons/amd-developer-hackathon-act-iii (SOURCED)
- Live dashboard: https://lablab.ai/ai-hackathons/amd-developer-hackathon-act-iii/live (SOURCED, snapshot 2026-10-08)
- Linked but NOT yet read: Hackathon Guidelines, Getting Started Guide, lablab.ai Hackathon Rule Book, Terms of Use section 16 (participation terms)

## What the event is
Hybrid hackathon. Everything runs in the cloud on AMD GPUs with the ROCm stack, so no local hardware is needed. Participants choose one business challenge and build a working product where AMD technology powers a meaningful part of it. Online build is open to everyone; selected participants can also join on-site in Rome, Milan or Imperia on 10-17/18 (travel and accommodation not covered; approval required).

## Tracks (event page)
1. Intelligent Industry: help factories spot problems earlier (failure prediction, defect detection, manual search, safety, waste).
2. Health and Wellbeing: make part of the patient journey safer or clearer; no autonomous diagnosis; show uncertainty and human review.
3. Reinvent Commerce: help a business understand customers and act (recommendations, support, demand planning); an LLM may not be the only forecasting method.
4. Create a New Kind of Experience: media, marketing or entertainment that adapts per audience; show at least two audiences, cost per experience and who pays.

Partner track: Evolus Business Agents on AMD (agent that runs a real business process end to end on Evolus, with an open model served on AMD through your own vLLM endpoint).
Partner awards: Evolus and Google technologies are optional; a project may qualify for the main prize, one partner prize, or both. Google's prize terms are not described on the page.

## Judging
Application of Technology, Presentation, Business Value, Originality. The demo must show the AMD component inside the working product.

## Discrepancies to resolve
- Build window: event page says 12-18 October; live page says 12-17 October. Submission deadline (10-18 15:00 UTC) is the same on the live page.
- Live page shows Tracks "TBA" and no tech partners; the event page lists four tracks and partners.
- Event schedule on the event page says "To be announced".
- Prize split per track is not shown.
- Whether work may start before kickoff is not stated here; the rule book may say.
