Shreyankkkkk/foundations/learning/ai/notes/Claude/Claude_101-1.md

# Source and attribution

These notes are my personal study notes based on Anthropic's Claude 101 course.

- Course: Claude 101
- Provider: Anthropic
- Source: https://anthropic.skilljar.com/
- Copyright: © 2025 Anthropic. All rights reserved.

## These notes are independently written summaries for educational and reference purposes and are not official Anthropic course materials.

# Meet Claude

---

## Lesson 1 : What is Claude

### Learning Objectives

- Explain what Claude is and the principles that guide its design
- Describe Claude's core capabilities and how it differs from a simple chatbot
- Identify the different ways to access Claude (web, desktop, and mobile)

---

### Course Roadmap

**1. Meet Claude**

> What is Claude, how do you talk to it, and how do you get great results?
> ↓
> **2. Organizing your work**
> Projects → Artifacts → Skills
> ↓
> **3. Expanding Claude's reach**
> Connectors → Enterprise Search → Research
> ↓
> **4. Putting it all together**
> Claude across roles → Where else can you work with Claude?
> ↓
> **5. Conclusion & certificate**
> Where do you go from here? → How do you earn your certificate?

---

### What is Claude?

- **Claude is an AI assistant and thinking partner**, not just a chatbot.
- Designed to help with a wide range of work tasks and complex problems.

---

#### Key characteristics

- **Helpful, harmless, and honest**
  - Guided by principles intended to avoid toxic/discriminatory outputs and assistance with illegal or unethical activities.
  - Uses **Constitutional AI** to align behavior with human values and promote transparent, reliable behavior.

- **More than a chatbot**
  - Can perform tasks such as:
    - Summarization
    - Search
    - Creative and collaborative writing
    - Q&A
    - Coding
    - Complex problem-solving
  - Designed to act as a **thinking partner** rather than simply provide answers.

- **Steerable and collaborative**
  - Can be directed on:
    - Personality
    - Tone
    - Behavior
  - Designed to be easier to converse with and more steerable, allowing users to get their desired output with less effort.

- **Available across devices**
  - Available on **web, desktop, and mobile**.
  - Available across **Free, Pro, Max, Team, and Enterprise** plans.
  - When signed in, **conversations, projects, memory, and preferences sync across devices**.

---

### Understanding Claude's capabilities

Claude can help with tasks that go beyond simple question-and-answer interactions. It can act as a **thinking partner** that both **automates** and **augments** your work.

---

#### Thinking partner vs. search box

The key difference is whether the request needs **your situation, context, judgment, or existing work**.

- A **search box** is best for:
  - Simple facts
  - Definitions
  - Calculations
  - Current information
  - Questions with one straightforward answer

- A **thinking partner** is best when:
  - Your own work or context is involved
  - The task requires judgment or reasoning
  - You want to transform or improve something you've created
  - You need to explore a problem collaboratively
  - You may need to provide feedback and refine the result

> **A search box takes a question. Claude takes the situation.**

---

#### Which requests need a thinking partner?

##### 1. Exchange rate

> "What's the exchange rate from US dollars to euros today?"

**Search-box territory**

- This requires one current fact from an authoritative source.
- Nothing about the user's specific situation changes the answer.
- A search engine or simple lookup is sufficient.

---

##### 2. Rewriting an update

> "Rewrite my update below so the delay reads as a decision, not an apology."

**Thinking-partner work**

- Claude needs to work with the user's existing draft.
- It must preserve the facts while making a judgment about tone and framing.
- The user can provide feedback and ask Claude to adjust the result.

**Key idea:** The task becomes collaborative because the user's content and judgment are part of the work.

---

##### 3. Structuring a quarterly business review

> "best structure for a quarterly business review presentation"

**Thinking-partner work — when context is provided**

- As written, this looks like a search query.
- A search engine can provide generic presentation templates.
- Claude becomes more useful when given the user's specific context.

**Better version:**

> "Here's last quarter's review and the two slides leadership pushed back on. Restructure the story for this quarter."

**Key idea:** The value comes from giving Claude the situation, not just asking for a generic answer.

---

##### 4. Understanding a customer's complaint

> "I've pasted a customer's complaint thread below. Help me work out what they're actually asking for before I reply."

**Thinking-partner work**

- There may be no external page or fact to look up.
- Claude needs to read and interpret the conversation.
- The user can correct Claude's interpretation and refine the understanding.

**Example:**

> "No, they're not after a refund. They want a firm date."

**Key idea:** The back-and-forth between the user and Claude is part of the task.

---

##### 5. Purchase order vs. invoice

> "What's the difference between a purchase order and an invoice?"

**Search-box territory**

- This is a straightforward definition.
- A search engine or Claude can provide the same basic explanation.
- The question does not require knowledge of the user's specific situation.

**It becomes thinking-partner work when context is added:**

> "A vendor sent us an invoice with no PO attached. Given how our team handles approvals, what should we do next?"

**Key idea:** Adding your real situation turns a general question into a problem that requires reasoning.

---

##### 6. Calculating working days

> "How many working days are there between March 3 and March 24?"

**Search-box territory**

- This can be answered directly with a calculation or calendar.
- There is no personal context for Claude to reason about.
- Not every request needs a thinking partner.

---
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
