Shreyankkkkk/foundations/projects/sumo-robot/design/cad-v2/WhatsApp Image 2026-09-25 at 10.48.38.jpeg

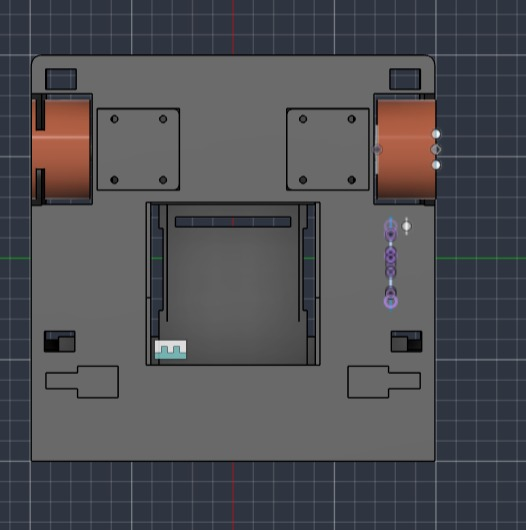
projects/sumo-robot/design/cad-v2/WhatsApp Image 2026-09-25 at 10.48.38.jpeg
