Shreyankkkkk/foundations/projects/sumo-robot/design/parametric/WhatsApp Image 2026-09-26 at 18.34.34.jpeg

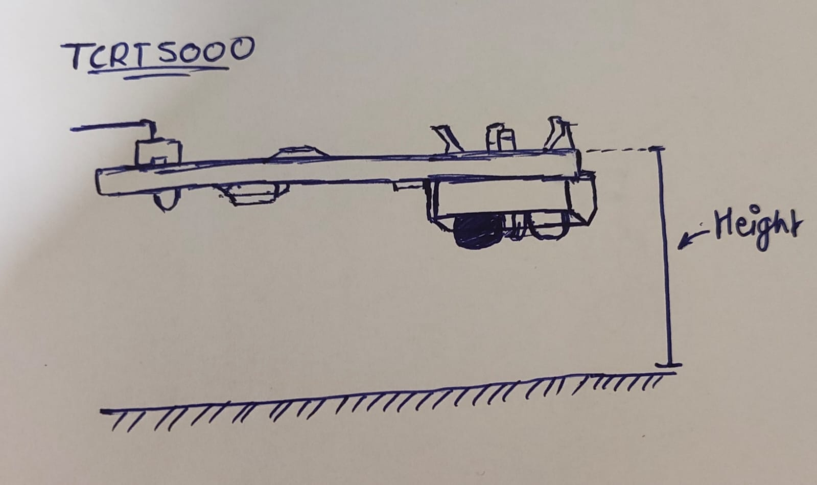
projects/sumo-robot/design/parametric/WhatsApp Image 2026-09-26 at 18.34.34.jpeg
