Shreyankkkkk/foundations/projects/sumo-robot/firmware/strategy/v2.4_Strategy/Motors.h

#ifndef MOTORS_H
#define MOTORS_H

void initMotors();          // enables drivers, PWM 0
void disableMotorDrivers(); // EN pins LOW, PWM 0: drivers fully off (pre-power-up state)
void stopMotors();
void drive(int leftSpeed, int rightSpeed, bool immediate = false); // -255..255; immediate=true bypasses the slew limiter

int getAppliedLeft();
int getAppliedRight();

#endif
